h13-0/RoboCup/ImageProcessing/YoloFastest/chart.png

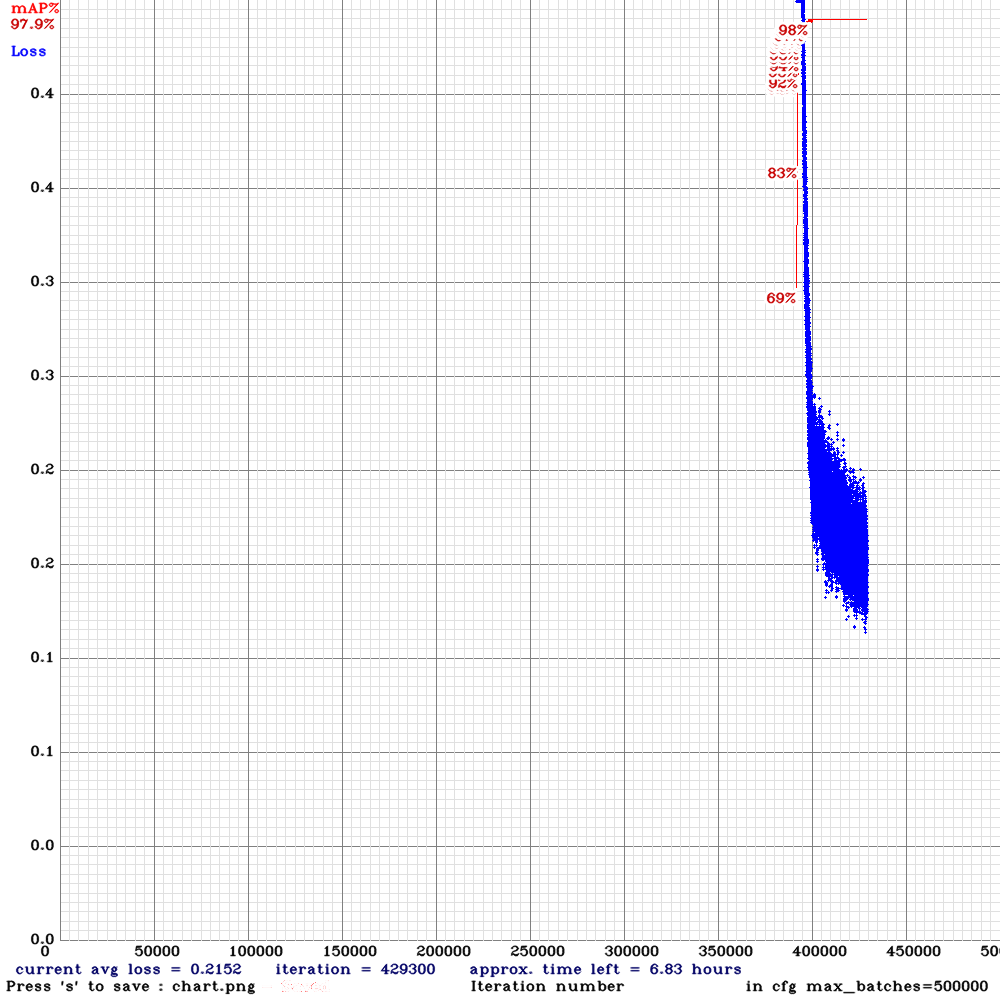
ImageProcessing/YoloFastest/chart.png
