h13-0/RoboCup/ImageProcessing/YoloV4Tiny/yoloV4TinyPreliminaryTrainWithHighBatch320/chart.png

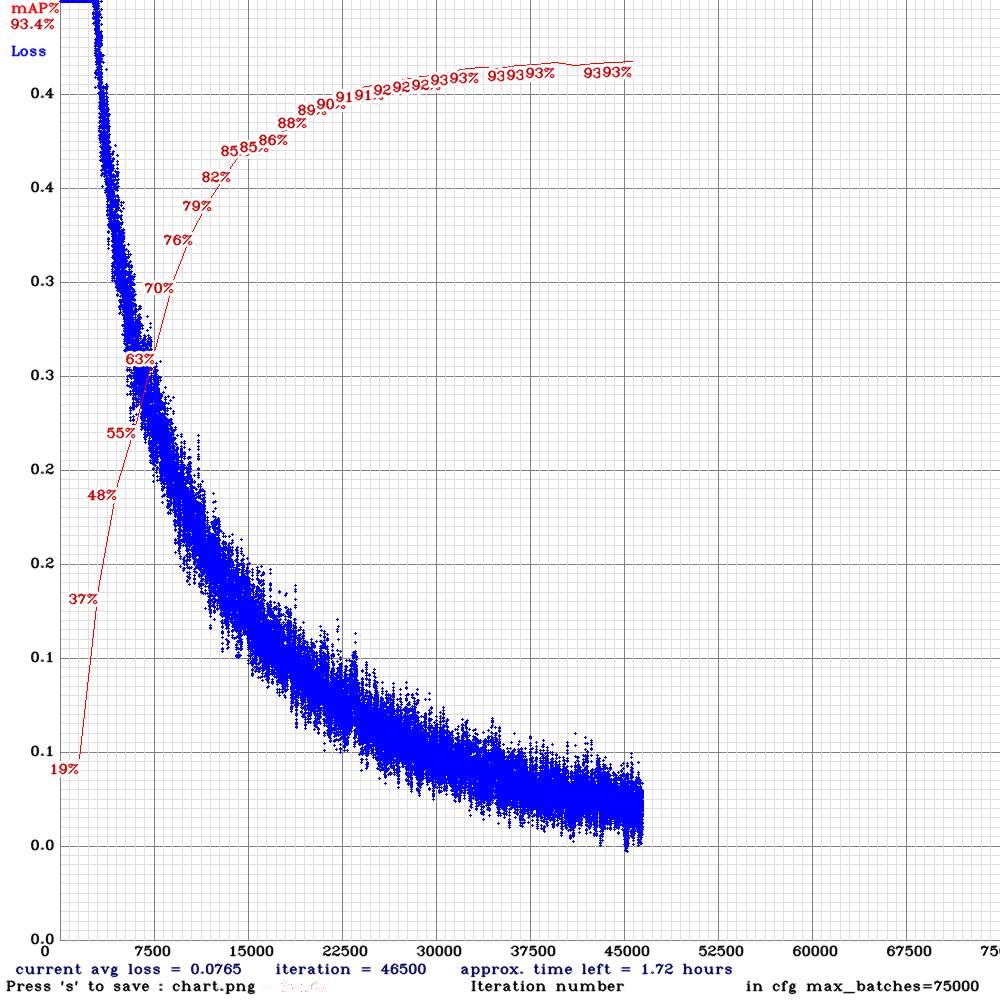
ImageProcessing/YoloV4Tiny/yoloV4TinyPreliminaryTrainWithHighBatch320/chart.png
