h13-0/RoboCup/ImageProcessing/YoloV4Tiny/yoloV4TinyRetrainWithRealScene320/predictions.jpg

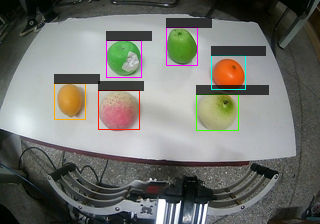
ImageProcessing/YoloV4Tiny/yoloV4TinyRetrainWithRealScene320/predictions.jpg
