h13-0/RoboCup/Images/LiftingPlatformAnnotationPicture1.jpg

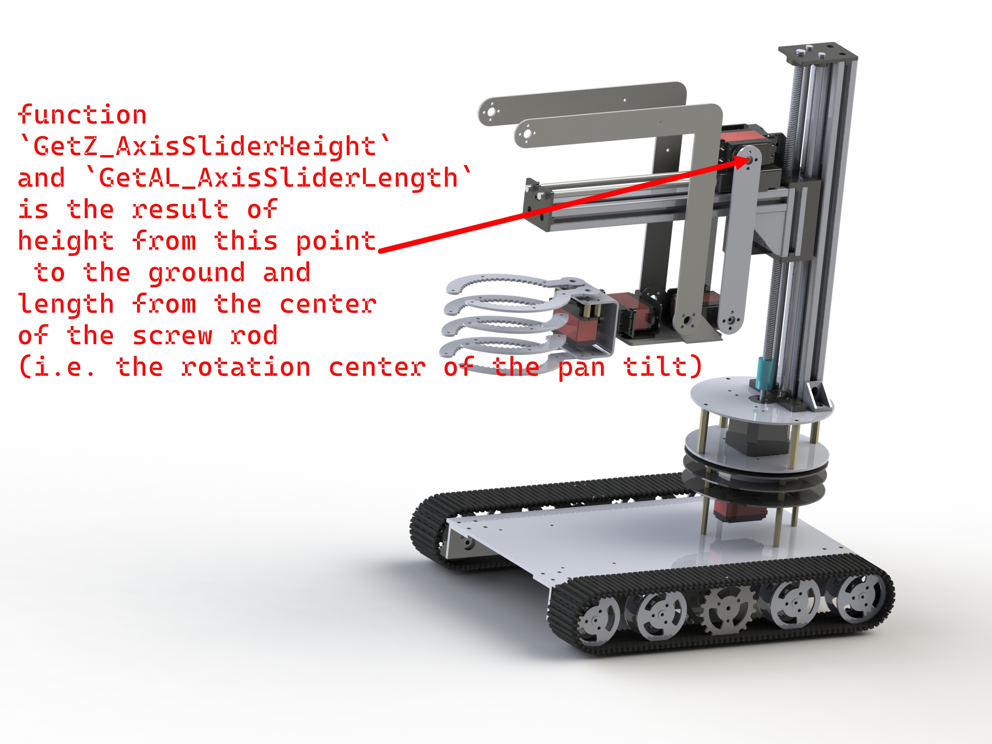
Images/LiftingPlatformAnnotationPicture1.jpg
