h13-0/RoboCup/Images/俯视图.JPG

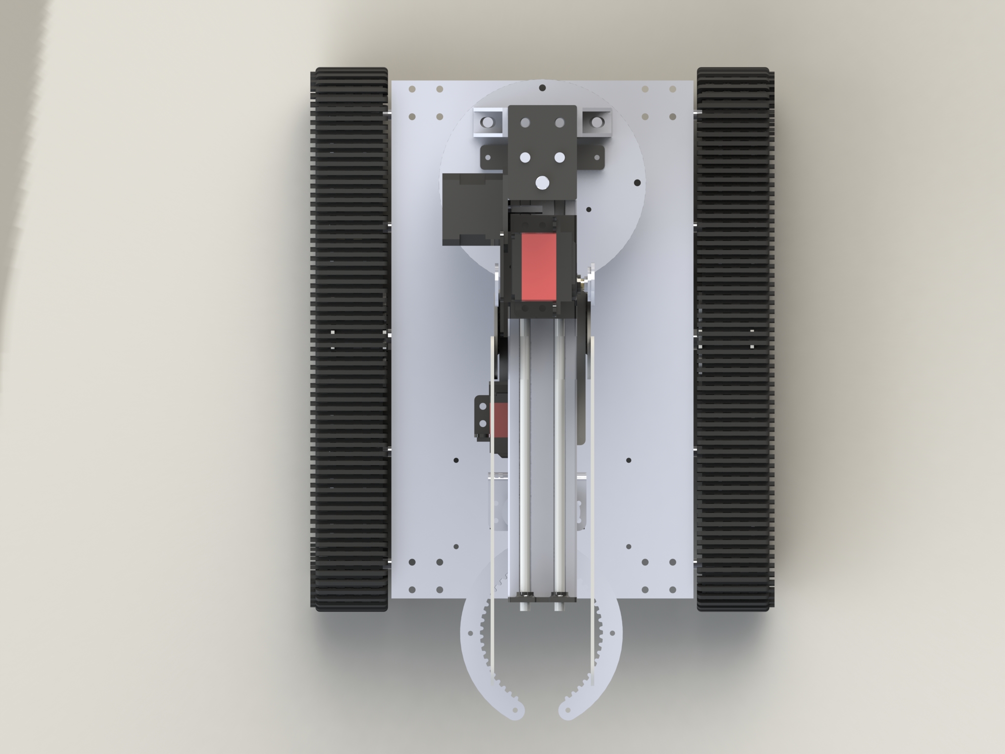
Images/俯视图.JPG
