h13-0/RoboCup/Images/左视图.JPG

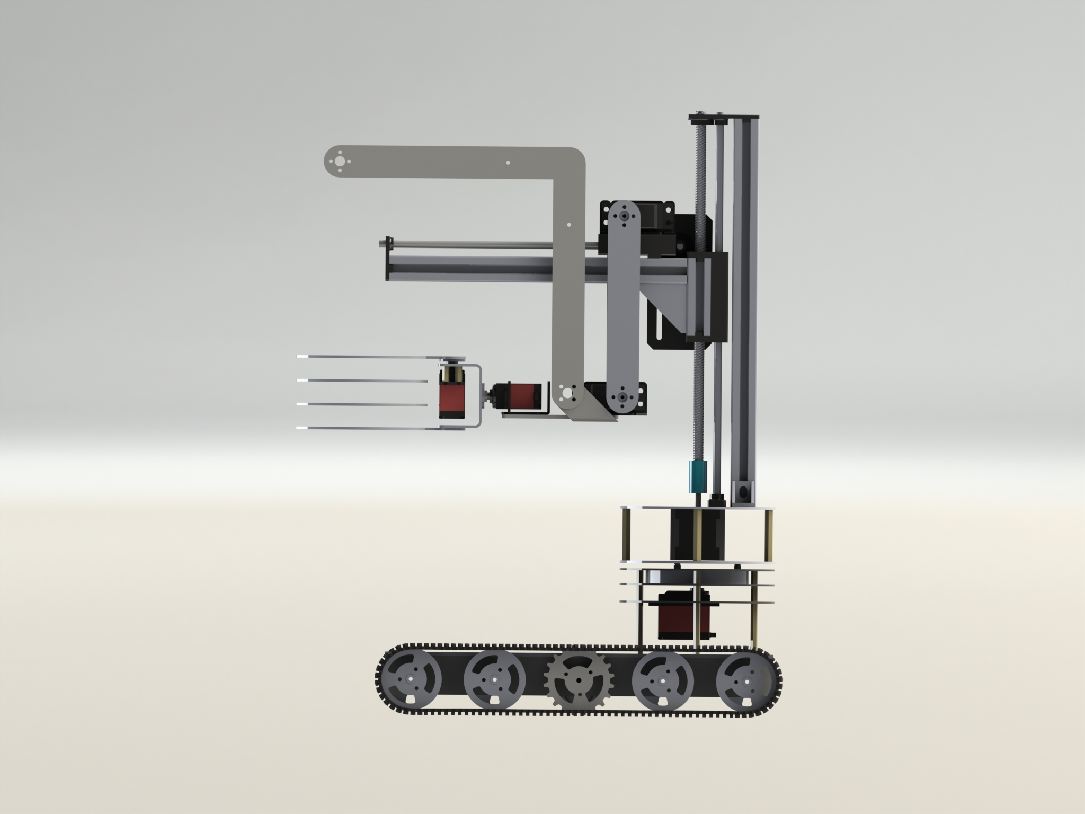
Images/左视图.JPG
