h13-0/RoboCup/Images/斜视图.JPG

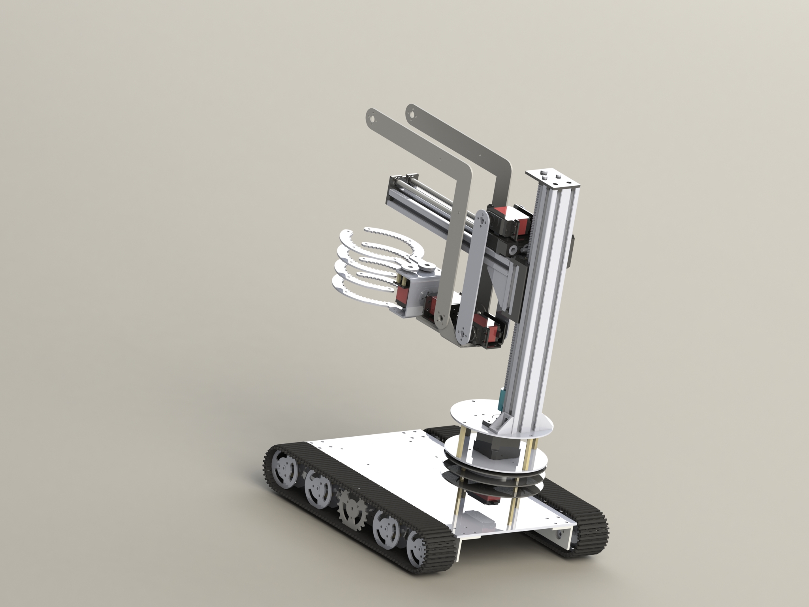
Images/斜视图.JPG
