h13-0/RoboCup/Machine/3D打印STL/磁铁竖向支架.STL

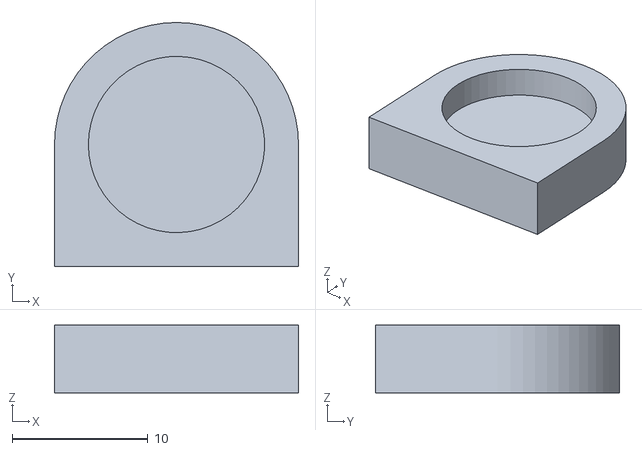
[picture p35: CAD file, 2021-08-29]
Machine/3D打印STL/磁铁竖向支架.STL
18.0 x 18.0 x 5.00
