h13-0/RoboCup/Machine/从动轮轴承.SLDPRT

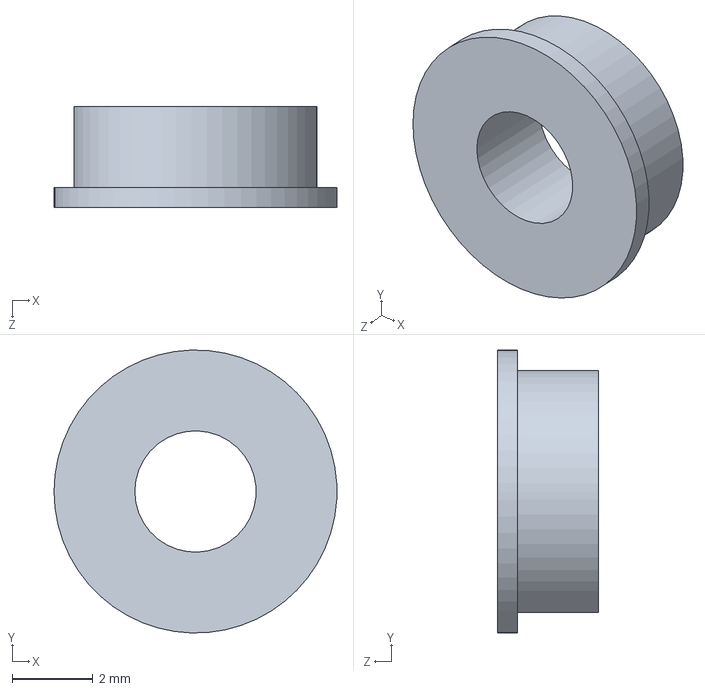
[picture p36: CAD file, 2022-04-09]
Machine/从动轮轴承.SLDPRT
7.00 x 7.00 x 2.50 mm
