h13-0/RoboCup/Machine/3D打印STL/霍尔传感器支架.STL

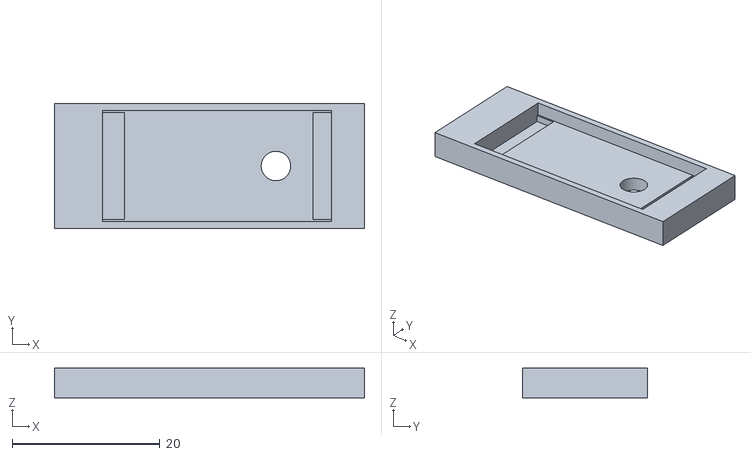
[picture p38: CAD file, 2021-08-29]
Machine/3D打印STL/霍尔传感器支架.STL
42.0 x 17.0 x 4.00
