h13-0/RoboCup/Machine/3429电机.SLDPRT

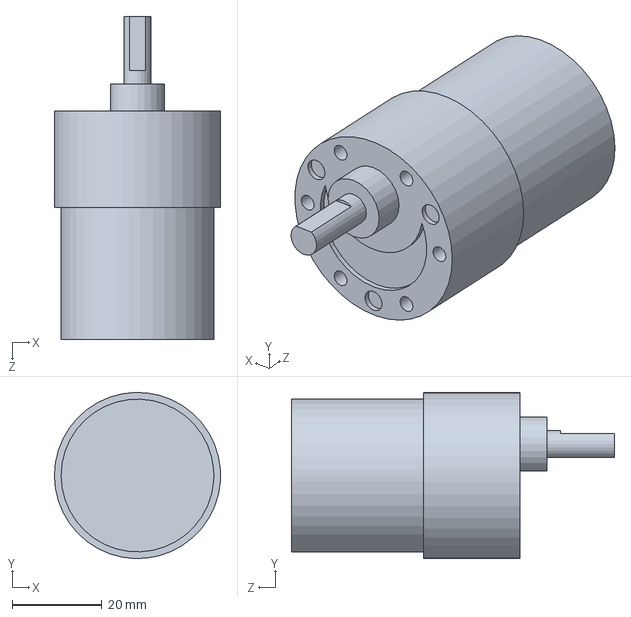
[picture p40: CAD file, 2022-04-09]
Machine/3429电机.SLDPRT
37.0 x 37.0 x 71.9 mm
