h13-0/RoboCup/Machine/3D打印STL/丝杆底支架.STL

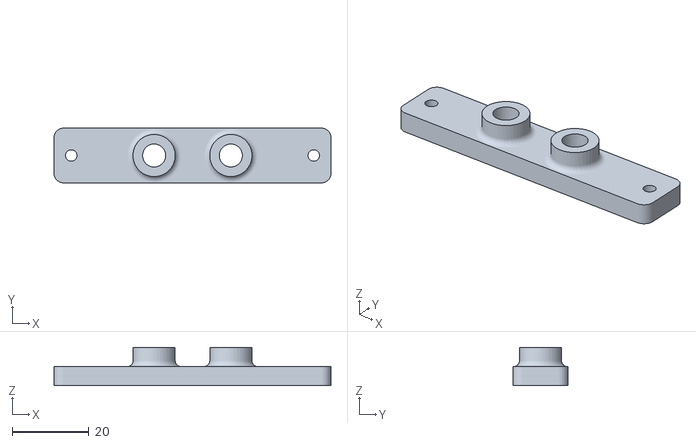
[picture p41: CAD file, 2021-08-23]
Machine/3D打印STL/丝杆底支架.STL
72.2 x 14.3 x 10.0
