h13-0/RoboCup/Machine/3D打印STL/丝杆滑块.STL

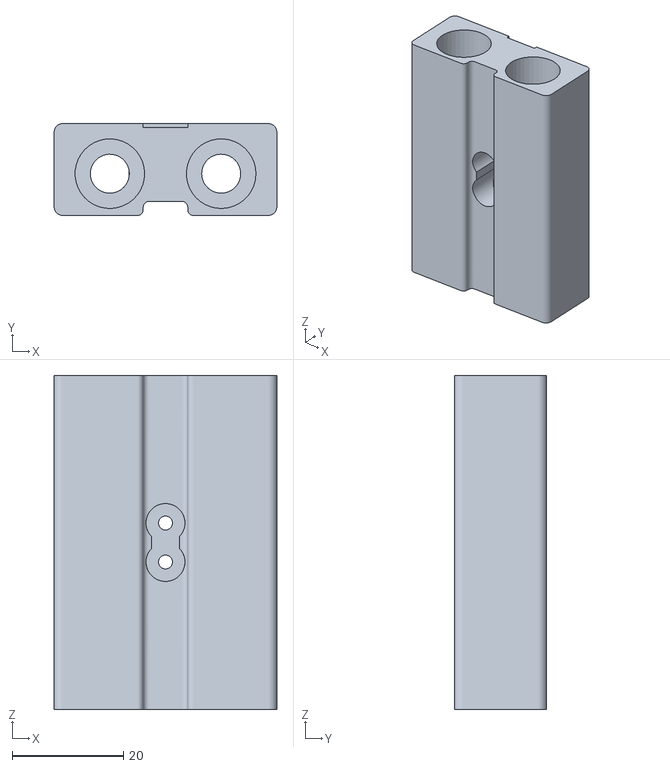
[picture p42: CAD file, 2021-08-23]
Machine/3D打印STL/丝杆滑块.STL
40.0 x 16.5 x 60.0
