h13-0/RoboCup/Machine/从动轮支杆.SLDPRT

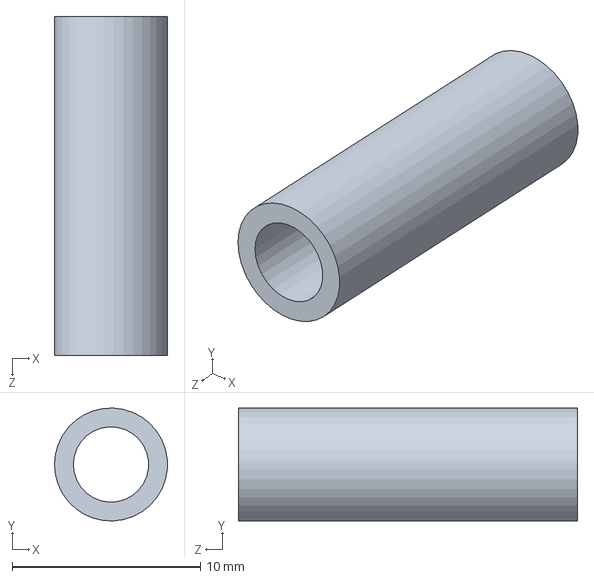
[picture p43: CAD file, 2022-04-09]
Machine/从动轮支杆.SLDPRT
6.00 x 5.99 x 18.0 mm
