h13-0/RoboCup/Machine/3D打印STL/直线轴承支架.STL

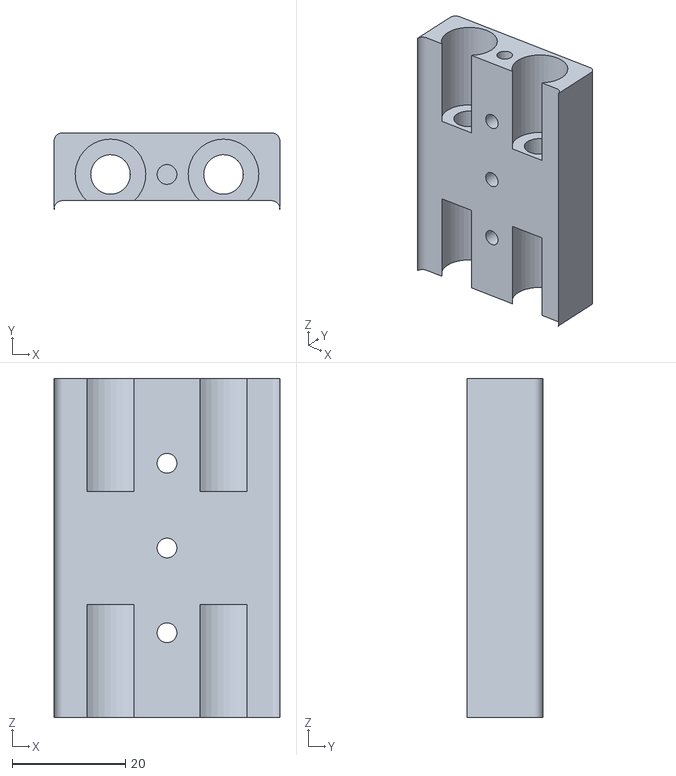
[picture p44: CAD file, 2021-08-23]
Machine/3D打印STL/直线轴承支架.STL
40.0 x 13.5 x 60.0
