h13-0/RoboCup/Machine/42步进.SLDPRT

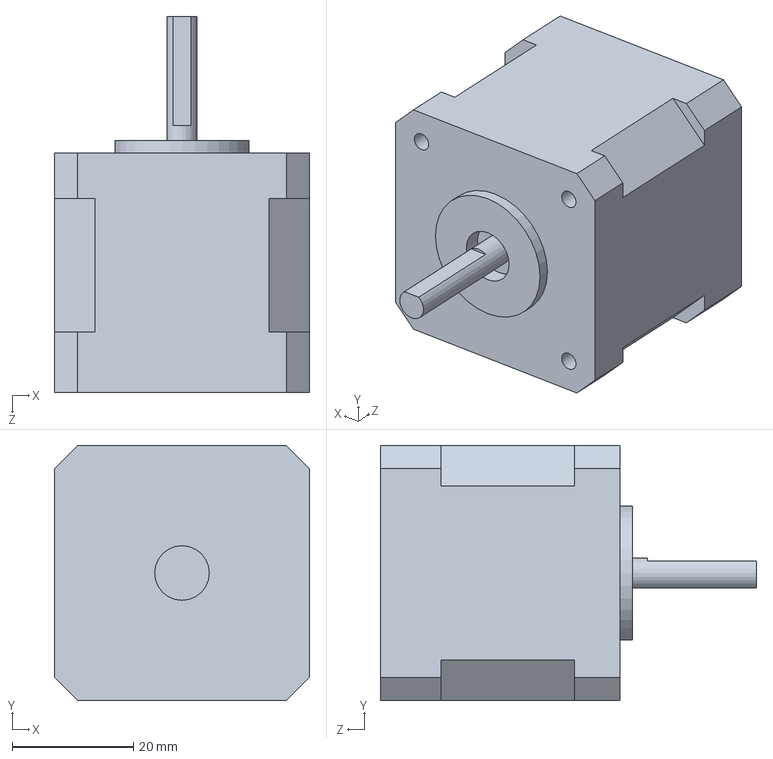
[picture p45: CAD file, 2022-04-09]
Machine/42步进.SLDPRT
42.0 x 42.0 x 62.0 mm
