h13-0/RoboCup/Machine/3D打印STL/侧TOF支架.STL

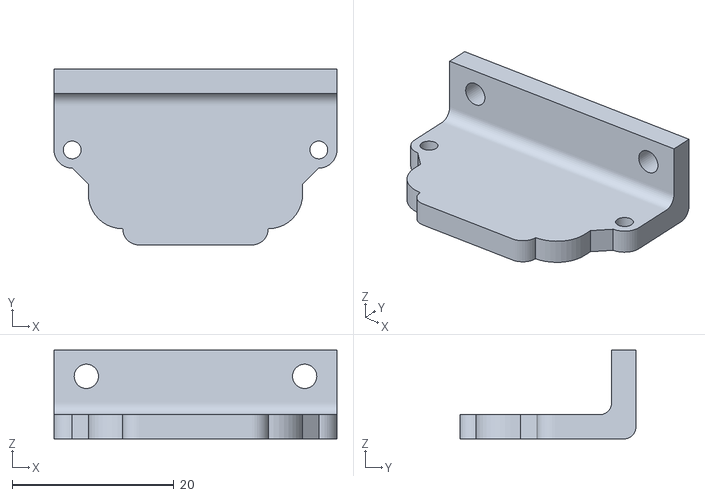
[picture p46: CAD file, 2021-08-23]
Machine/3D打印STL/侧TOF支架.STL
35.0 x 21.8 x 11.0
