h13-0/RoboCup/Machine/3D打印STL/丝杆顶支架.STL

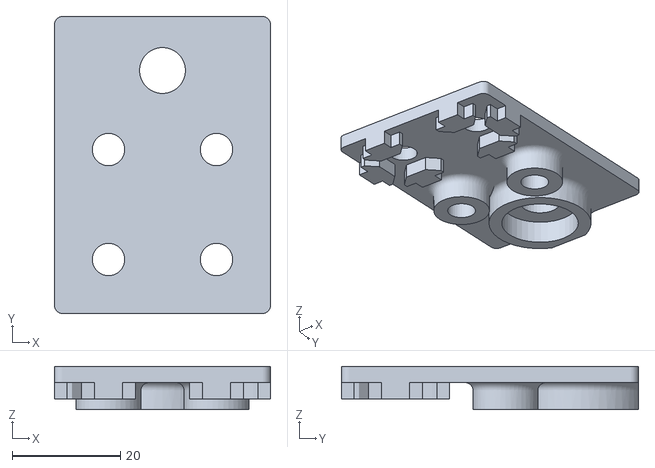
[picture p47: CAD file, 2021-08-23]
Machine/3D打印STL/丝杆顶支架.STL
40.0 x 55.0 x 8.00
