h13-0/RoboCup/Machine/M4铜柱40mm.SLDPRT

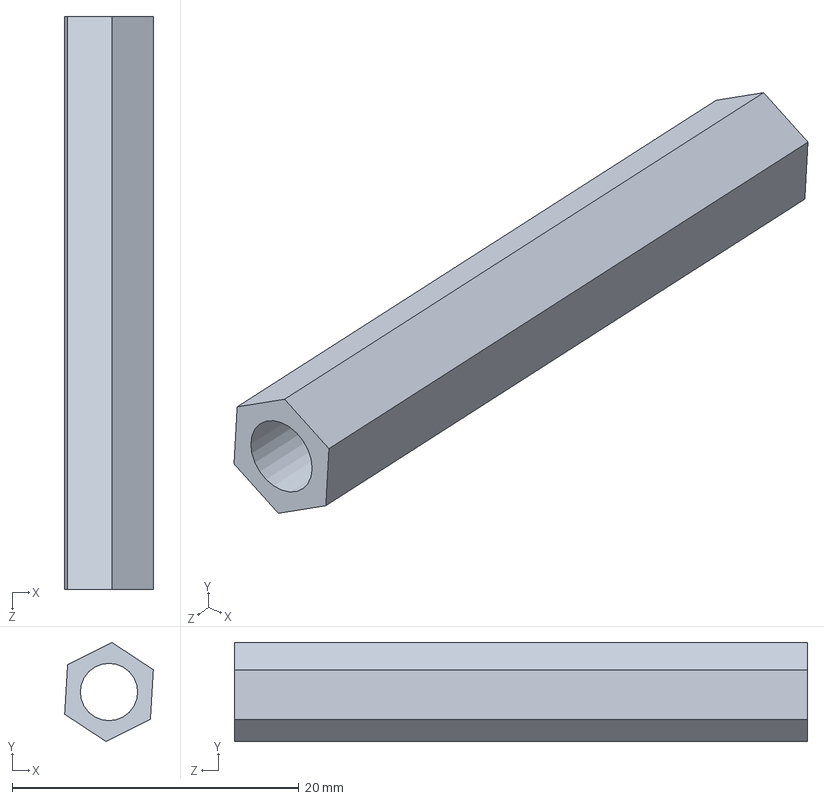
[picture p48: CAD file, 2022-04-09]
Machine/M4铜柱40mm.SLDPRT
6.19 x 6.92 x 40.0 mm
