h13-0/RoboCup/Machine/3D打印STL/丝杆滑台外支架.STL

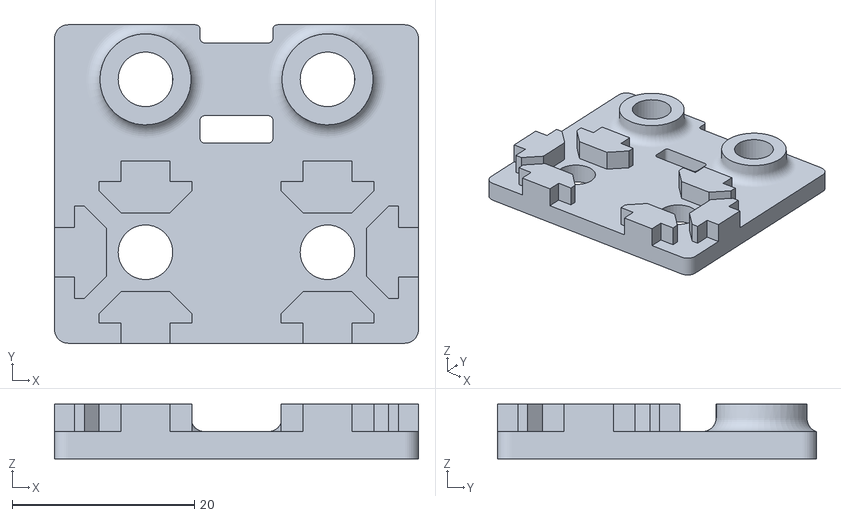
[picture p49: CAD file, 2021-08-23]
Machine/3D打印STL/丝杆滑台外支架.STL
40.0 x 35.0 x 6.00
