h13-0/RoboCup/Machine/M3紧固螺丝.SLDPRT

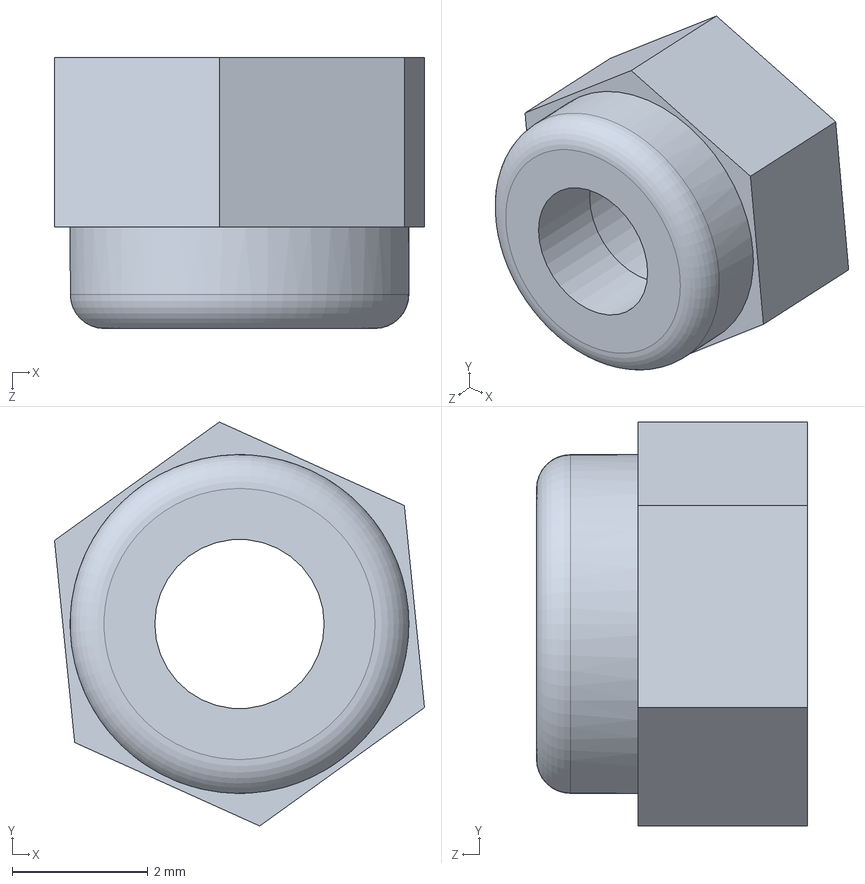
[picture p50: CAD file, 2022-04-09]
Machine/M3紧固螺丝.SLDPRT
5.46 x 5.96 x 4.00 mm
