h13-0/RoboCup/Machine/2040铝型材300mm.SLDPRT

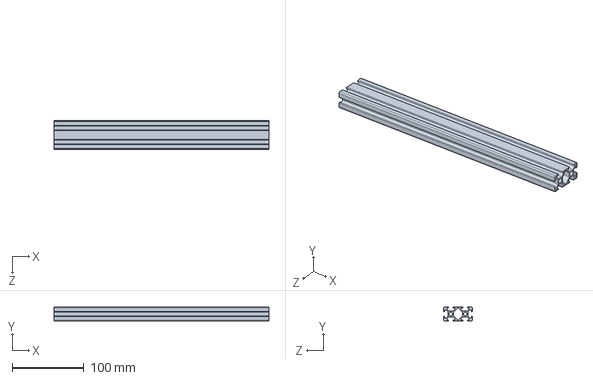
[picture p51: CAD file, 2022-04-09]
Machine/2040铝型材300mm.SLDPRT
300.0 x 20.0 x 40.0 mm
