h13-0/RoboCup/Machine/3D打印STL/同步带轴承支架.STL

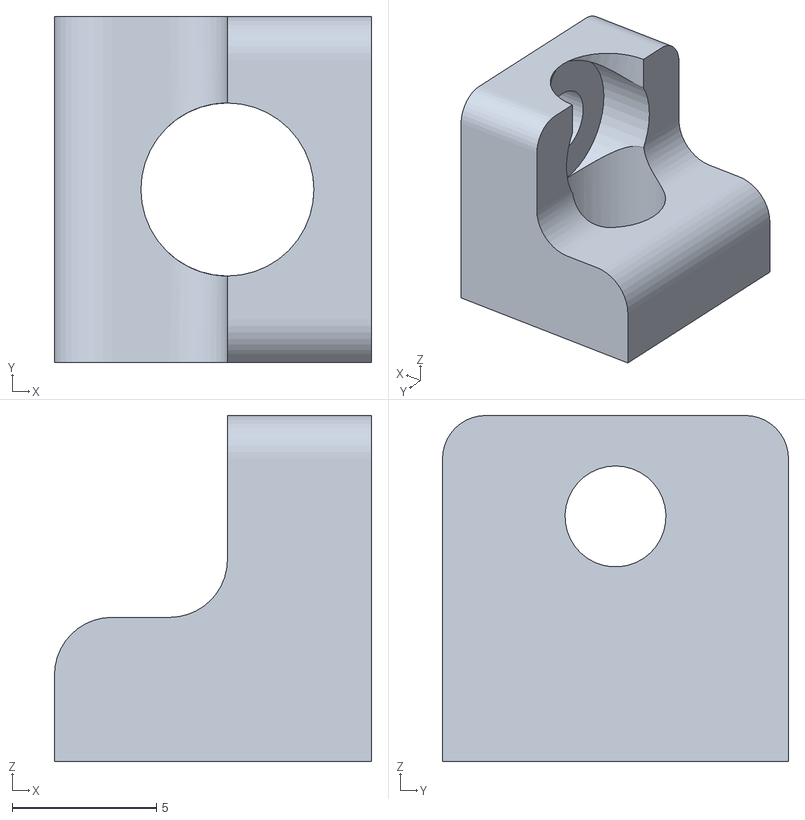
[picture p52: CAD file, 2021-08-23]
Machine/3D打印STL/同步带轴承支架.STL
11.0 x 12.0 x 12.0
