h13-0/RoboCup/Machine/3D打印STL/丝杆螺母支架.STL

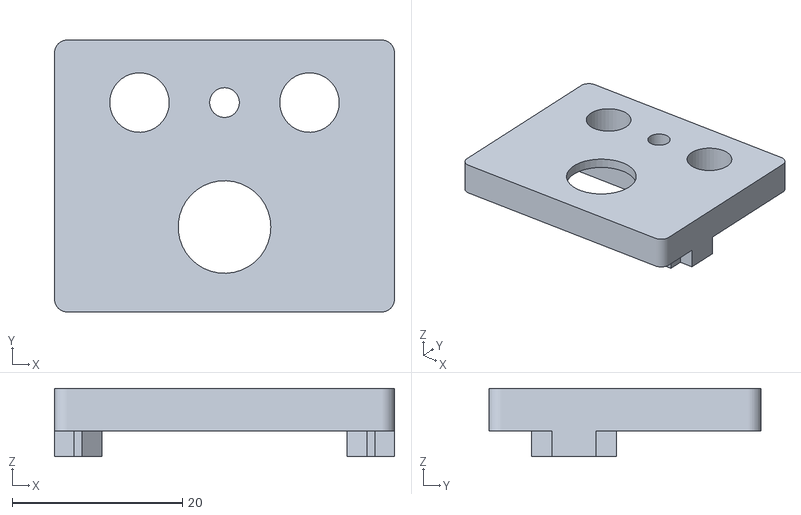
[picture p53: CAD file, 2021-08-23]
Machine/3D打印STL/丝杆螺母支架.STL
40.0 x 32.0 x 8.00
