h13-0/RoboCup/Machine/3D打印STL/电池垫板.STL

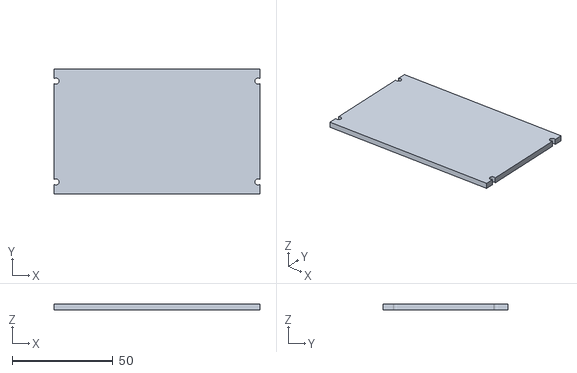
[picture p54: CAD file, 2021-08-23]
Machine/3D打印STL/电池垫板.STL
102.0 x 62.0 x 3.00
