h13-0/RoboCup/Machine/6mm滑杆307mm.SLDPRT

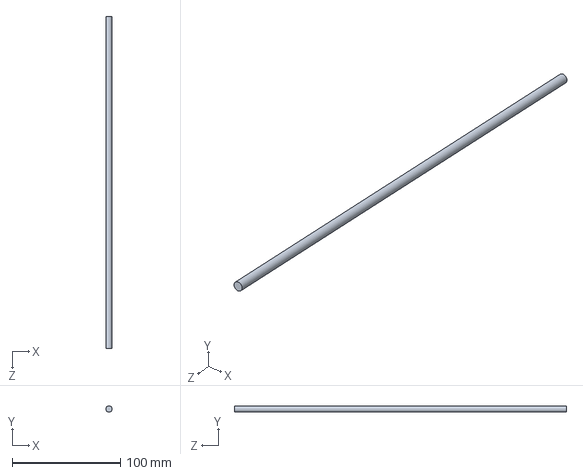
[picture p55: CAD file, 2022-04-09]
Machine/6mm滑杆307mm.SLDPRT
6.00 x 6.00 x 307.0 mm
