h13-0/RoboCup/Machine/3D打印STL/丝杆滑台内支架.STL

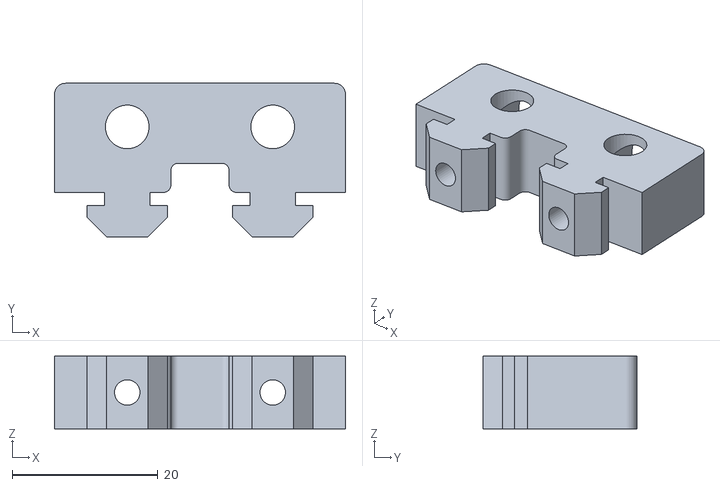
[picture p56: CAD file, 2021-08-23]
Machine/3D打印STL/丝杆滑台内支架.STL
40.0 x 21.1 x 10.0
