h13-0/RoboCup/Machine/M4大垫片.SLDPRT

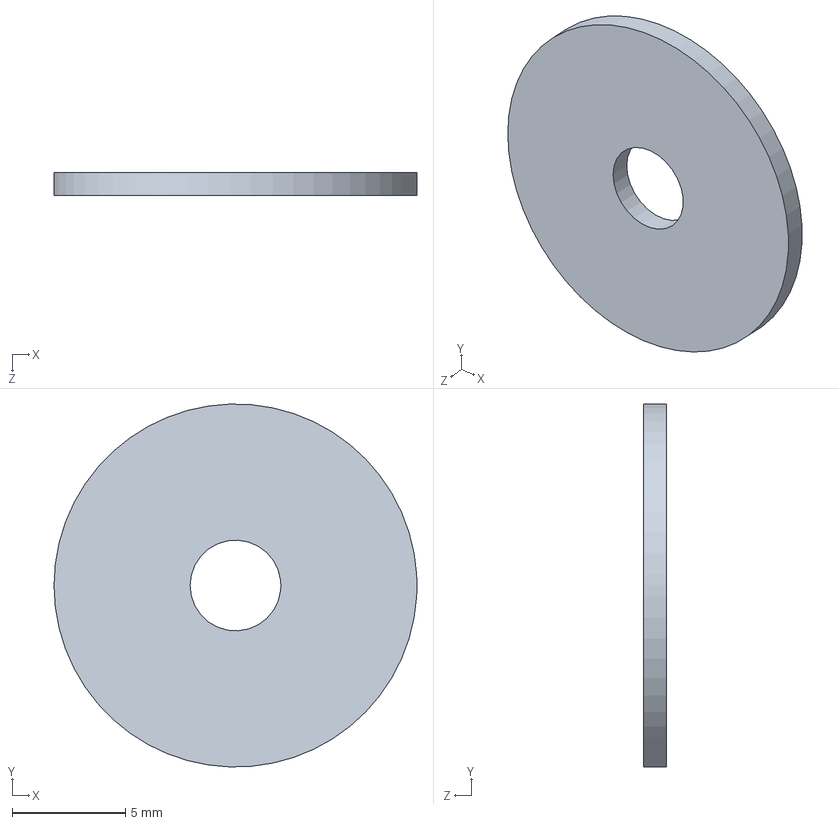
[picture p57: CAD file, 2022-04-09]
Machine/M4大垫片.SLDPRT
16.0 x 16.0 x 1.00 mm
