h13-0/RoboCup/Machine/3D打印STL/TOFSuppter.STL

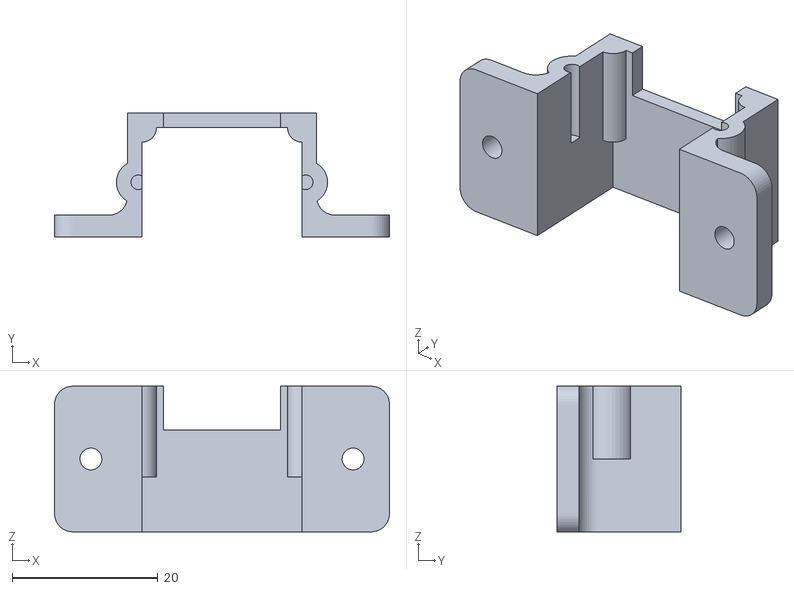
[picture p58: CAD file, 2021-06-14]
Machine/3D打印STL/TOFSuppter.STL
46.0 x 17.0 x 20.0
