h13-0/RoboCup/Machine/电机支架.SLDPRT

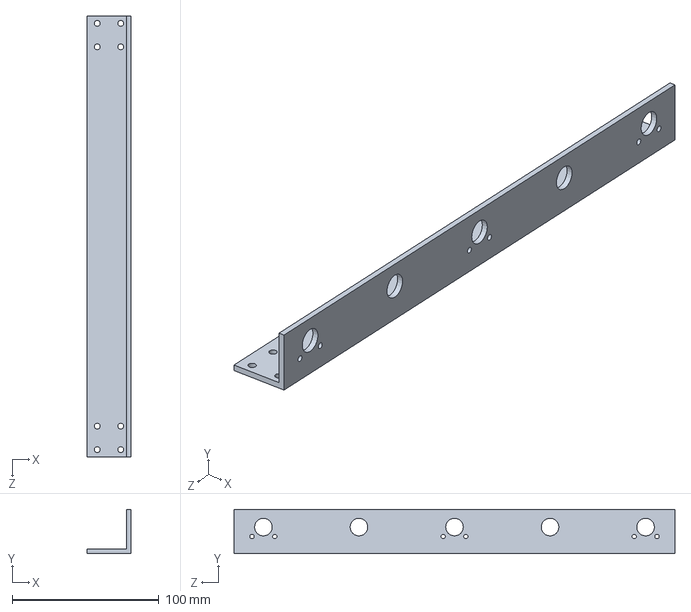
[picture p59: CAD file, 2022-04-09]
Machine/电机支架.SLDPRT
30.0 x 30.0 x 300.0 mm
