h13-0/RoboCup/Machine/M3铜柱10mm.SLDPRT

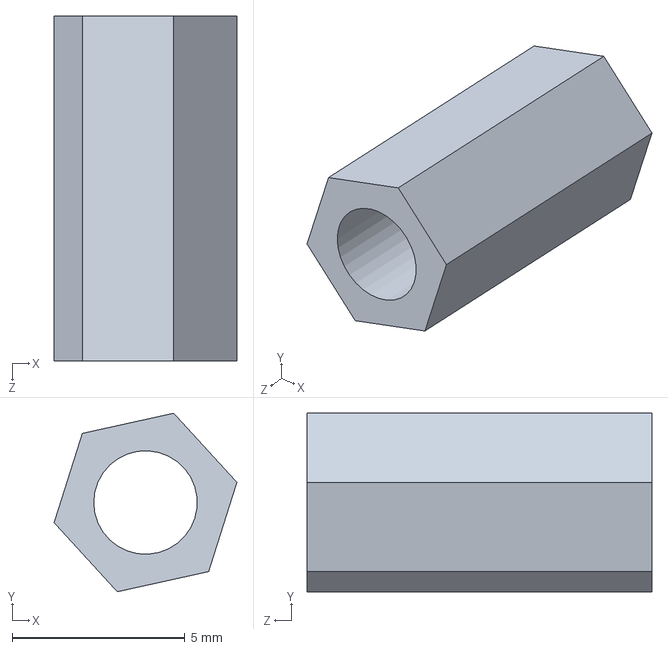
[picture p60: CAD file, 2022-04-09]
Machine/M3铜柱10mm.SLDPRT
5.30 x 5.17 x 10.0 mm
