h13-0/RoboCup/Machine/42步进35mm.SLDPRT

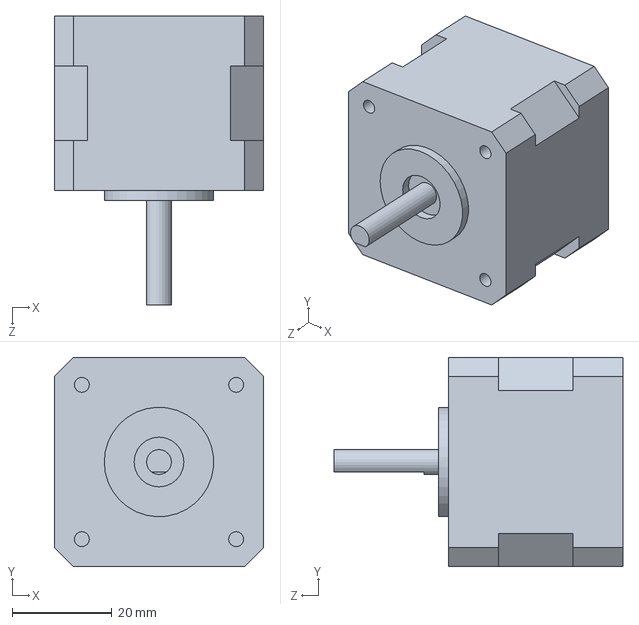
[picture p61: CAD file, 2022-04-09]
Machine/42步进35mm.SLDPRT
42.0 x 42.0 x 58.0 mm
