h13-0/RoboCup/Machine/8mm丝杆轴承.SLDPRT

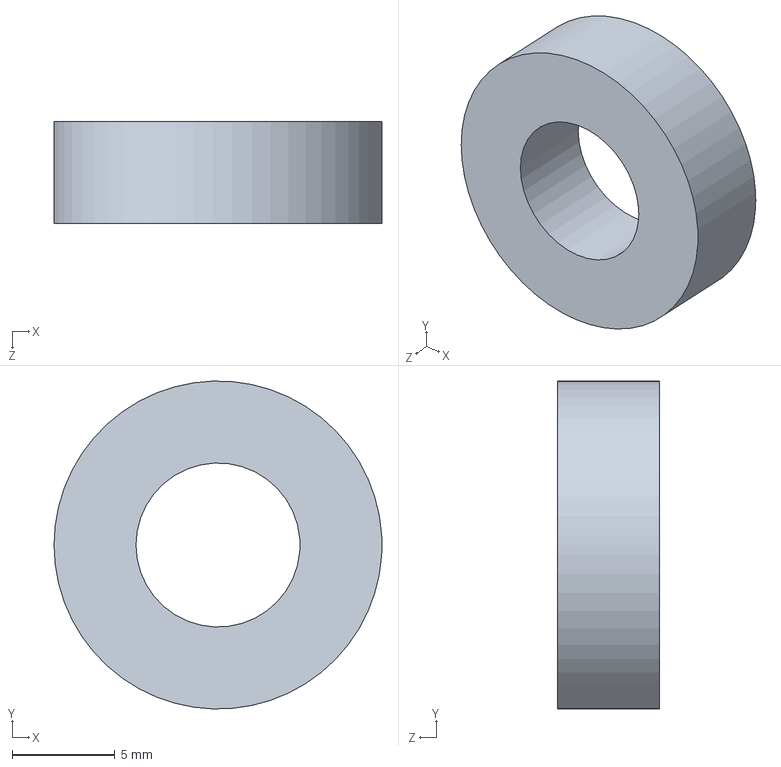
[picture p62: CAD file, 2022-04-09]
Machine/8mm丝杆轴承.SLDPRT
16.0 x 16.0 x 5.00 mm
