h13-0/RoboCup/Machine/42步进支架.SLDPRT

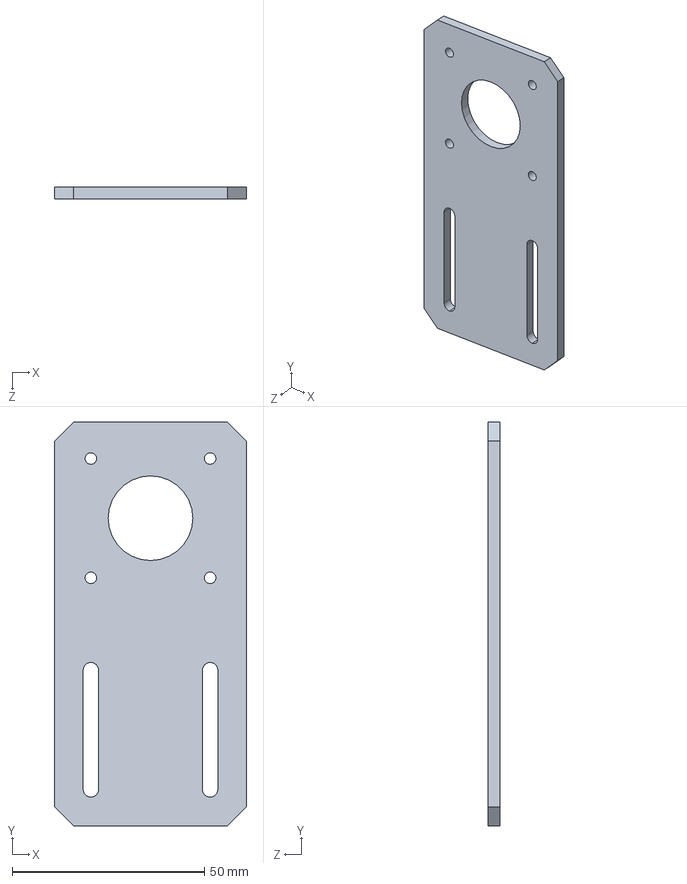
[picture p63: CAD file, 2022-04-09]
Machine/42步进支架.SLDPRT
50.0 x 105.0 x 3.00 mm
