h13-0/RoboCup/Machine/6mm滑杆220mm.SLDPRT

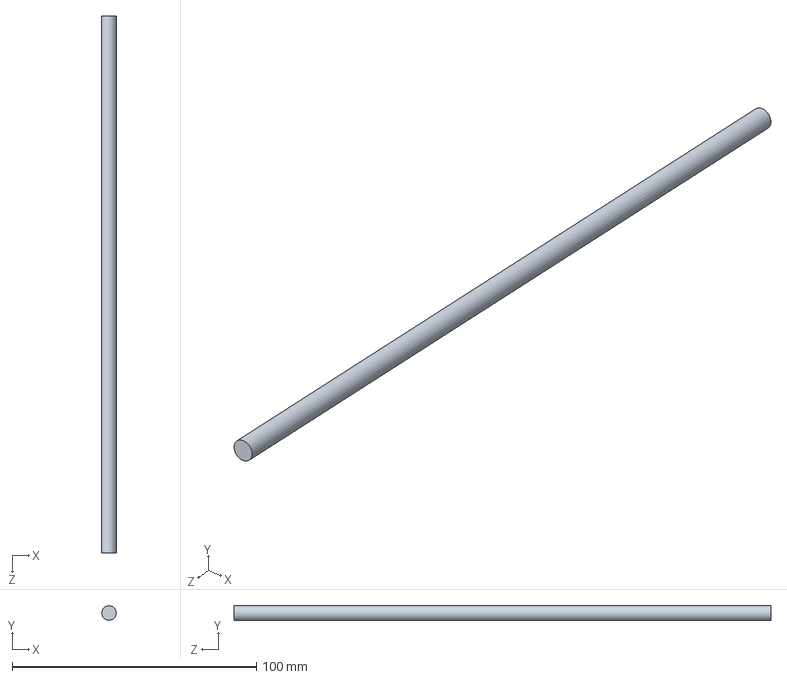
[picture p64: CAD file, 2022-04-09]
Machine/6mm滑杆220mm.SLDPRT
6.00 x 6.00 x 220.0 mm
