h13-0/RoboCup/Machine/M3铜柱17mm.SLDPRT

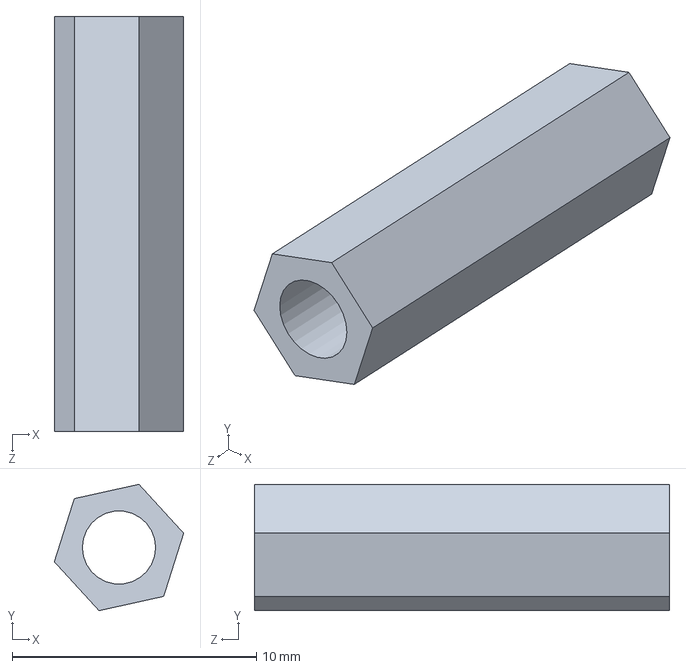
[picture p65: CAD file, 2022-04-09]
Machine/M3铜柱17mm.SLDPRT
5.30 x 5.17 x 17.0 mm
