h13-0/RoboCup/Machine/舵机圆盘.SLDPRT

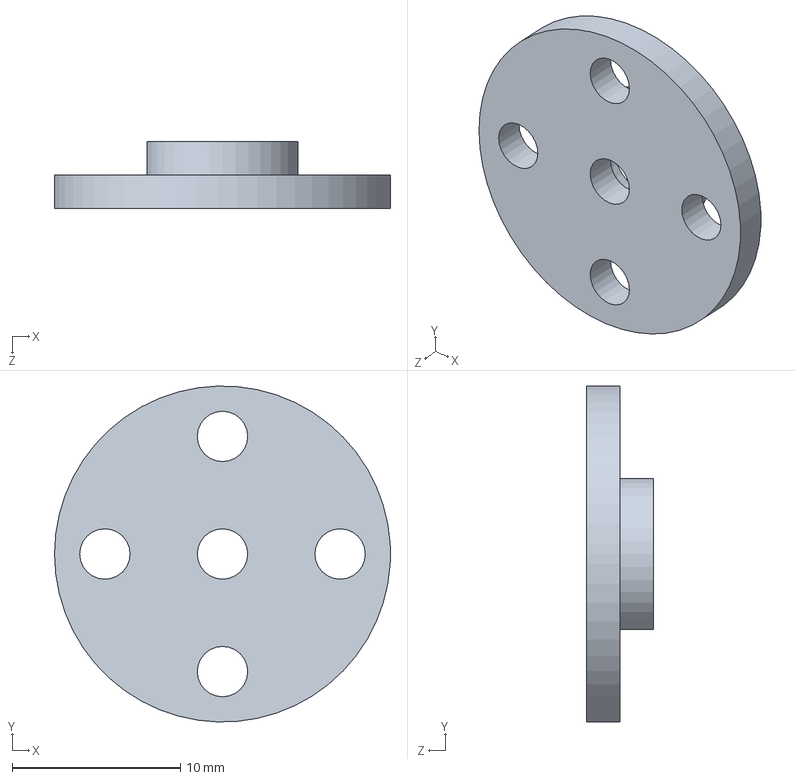
[picture p66: CAD file, 2022-04-09]
Machine/舵机圆盘.SLDPRT
20.0 x 20.0 x 4.00 mm
