h13-0/RoboCup/Machine/2040铝型材230mm.SLDPRT

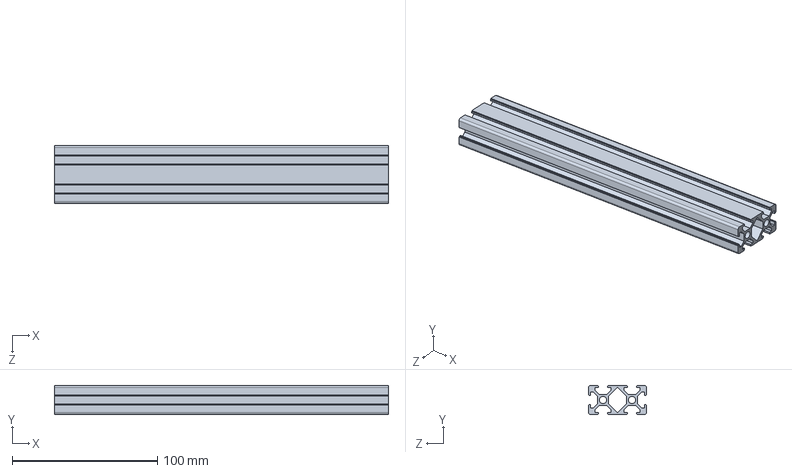
[picture p67: CAD file, 2022-04-09]
Machine/2040铝型材230mm.SLDPRT
230.0 x 20.0 x 40.0 mm
