h13-0/RoboCup/Machine/M3铜柱39.5mm.SLDPRT

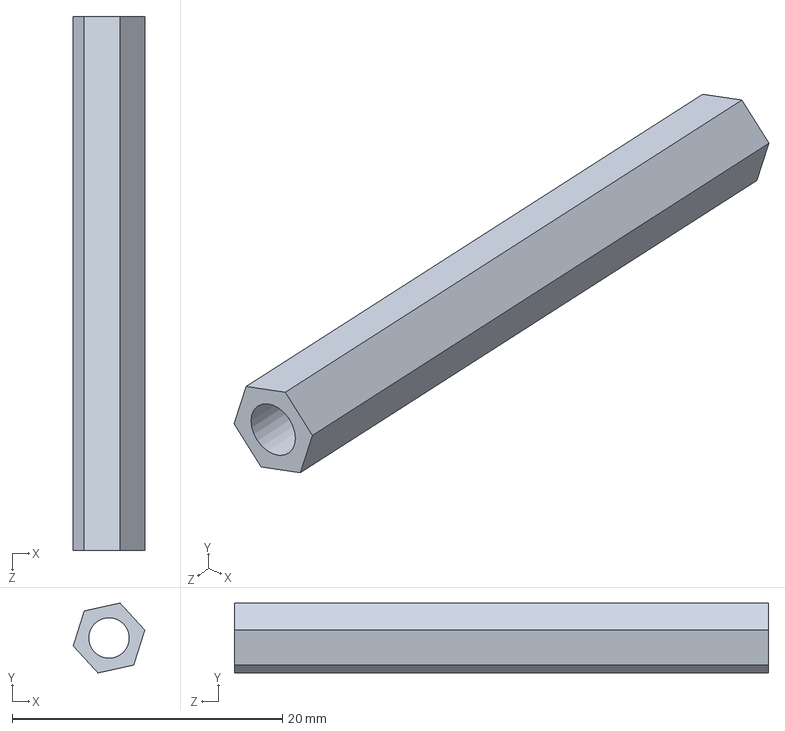
[picture p68: CAD file, 2022-04-09]
Machine/M3铜柱39.5mm.SLDPRT
5.30 x 5.17 x 39.5 mm
