h13-0/RoboCup/Machine/2020角件.SLDPRT

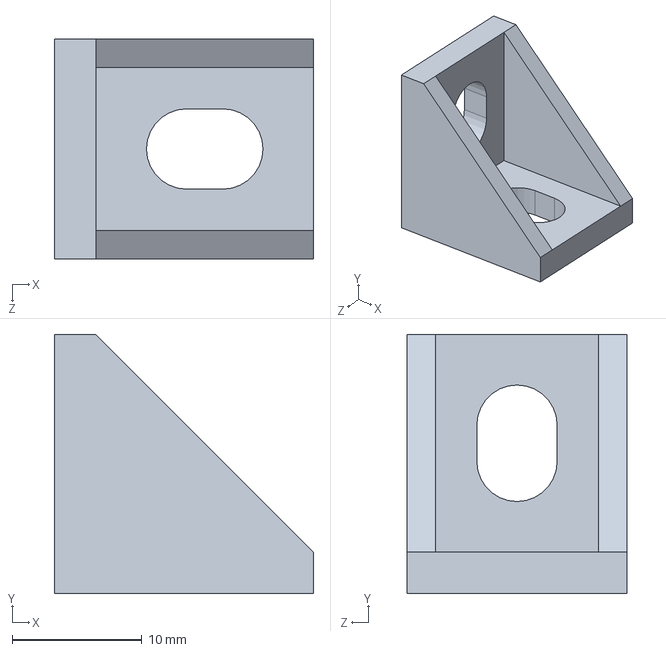
[picture p69: CAD file, 2022-04-09]
Machine/2020角件.SLDPRT
20.0 x 20.0 x 17.0 mm
