h13-0/RoboCup/Machine/从动轮间隔杆.SLDPRT

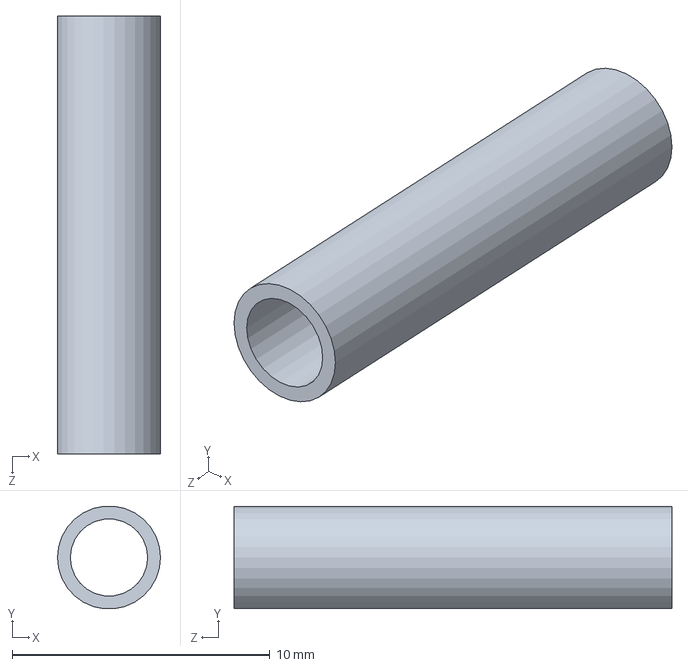
[picture p70: CAD file, 2022-04-09]
Machine/从动轮间隔杆.SLDPRT
4.00 x 3.98 x 17.0 mm
