h13-0/RoboCup/Machine/2040角件.SLDPRT

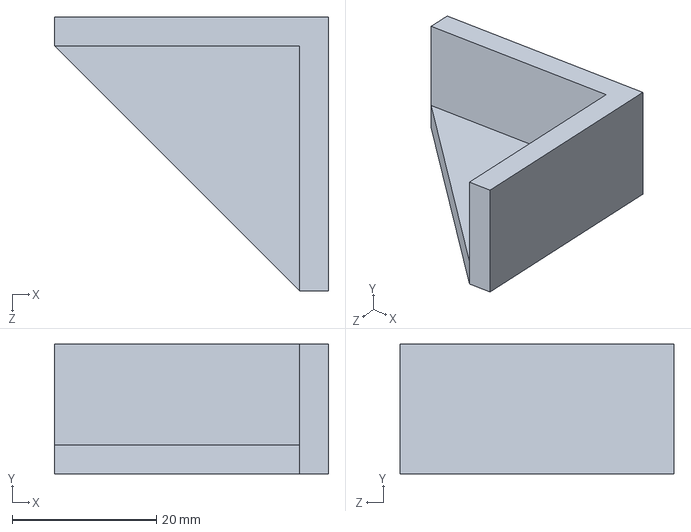
[picture p71: CAD file, 2022-04-09]
Machine/2040角件.SLDPRT
38.0 x 18.0 x 38.0 mm
