h13-0/RoboCup/Machine/车板铝板.SLDPRT

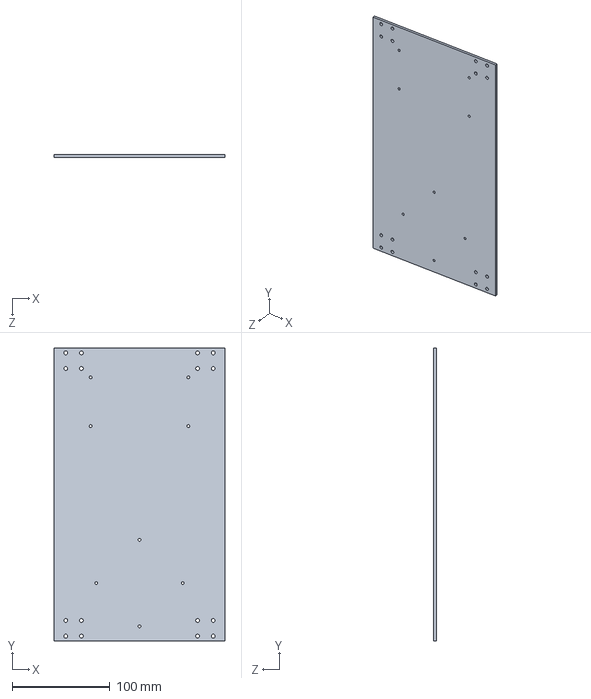
[picture p72: CAD file, 2022-04-09]
Machine/车板铝板.SLDPRT
175.0 x 300.0 x 3.00 mm
