h13-0/RoboCup/Machine/16齿同步轮.SLDPRT

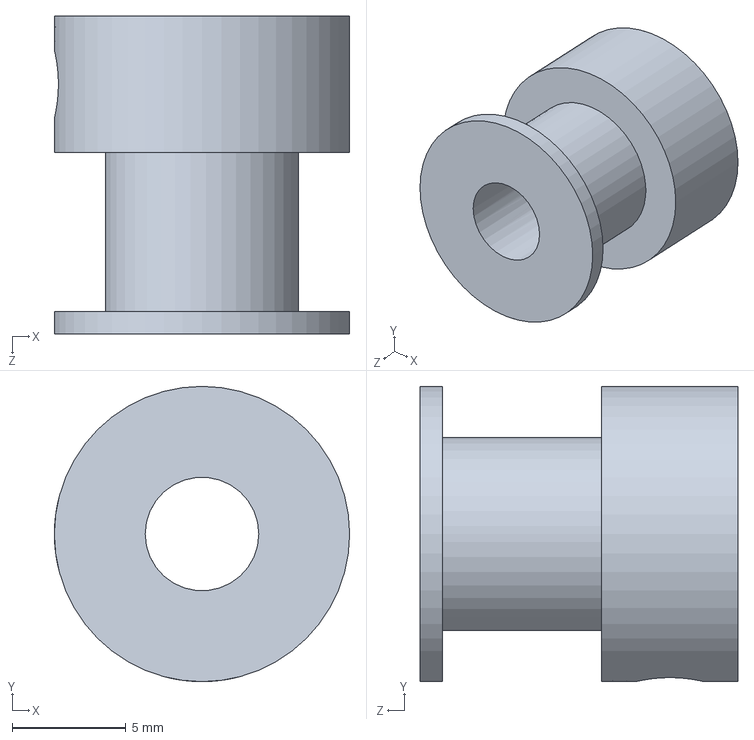
[picture p73: CAD file, 2022-04-09]
Machine/16齿同步轮.SLDPRT
13.0 x 13.0 x 14.0 mm
