h13-0/RoboCup/Machine/舵机斜U支架.SLDPRT

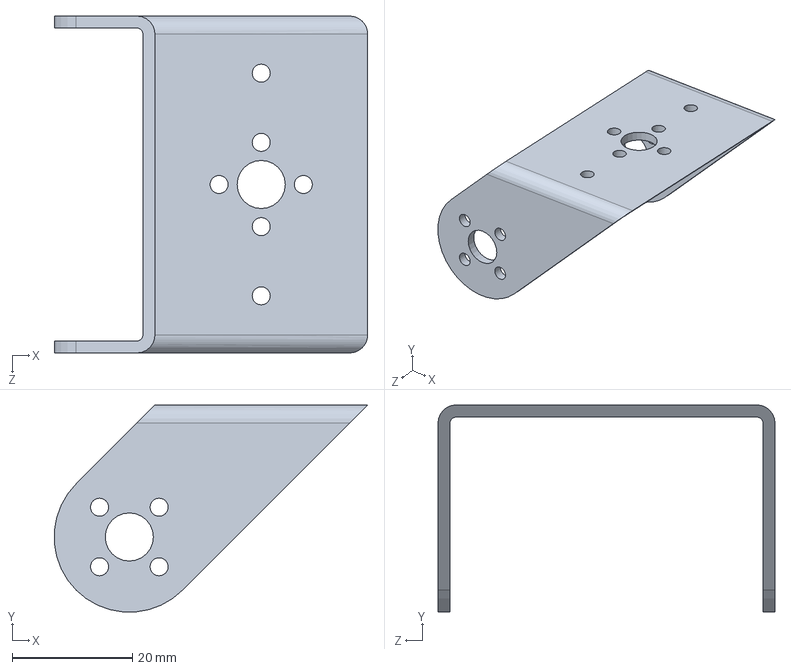
[picture p74: CAD file, 2022-04-09]
Machine/舵机斜U支架.SLDPRT
52.1 x 34.4 x 56.0 mm
