h13-0/RoboCup/Machine/M3铜柱32mm.SLDPRT

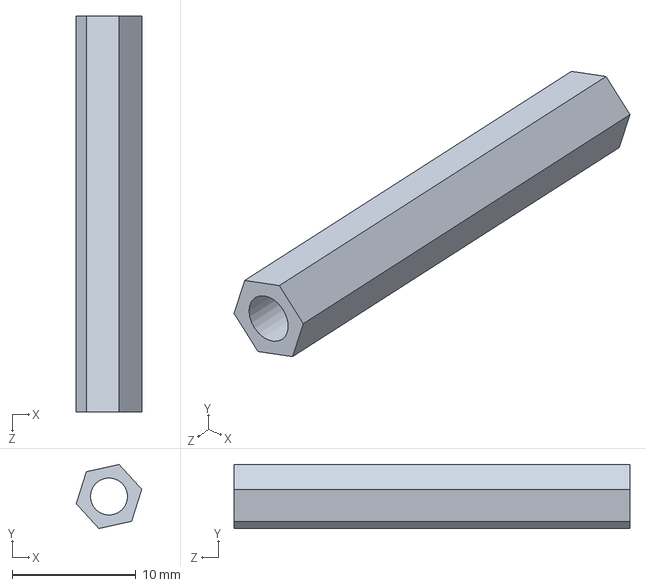
[picture p75: CAD file, 2022-04-09]
Machine/M3铜柱32mm.SLDPRT
5.30 x 5.17 x 32.0 mm
