h13-0/RoboCup/Machine/L形件.SLDPRT

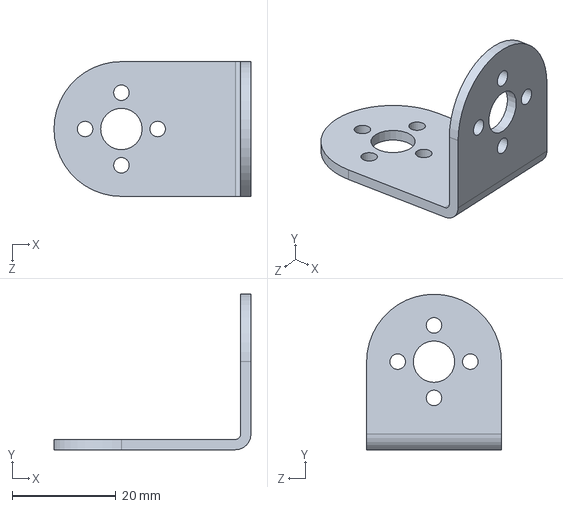
[picture p76: CAD file, 2022-04-09]
Machine/L形件.SLDPRT
38.0 x 30.0 x 26.0 mm
