h13-0/RoboCup/Machine/8mmx4丝杆285mm.SLDPRT

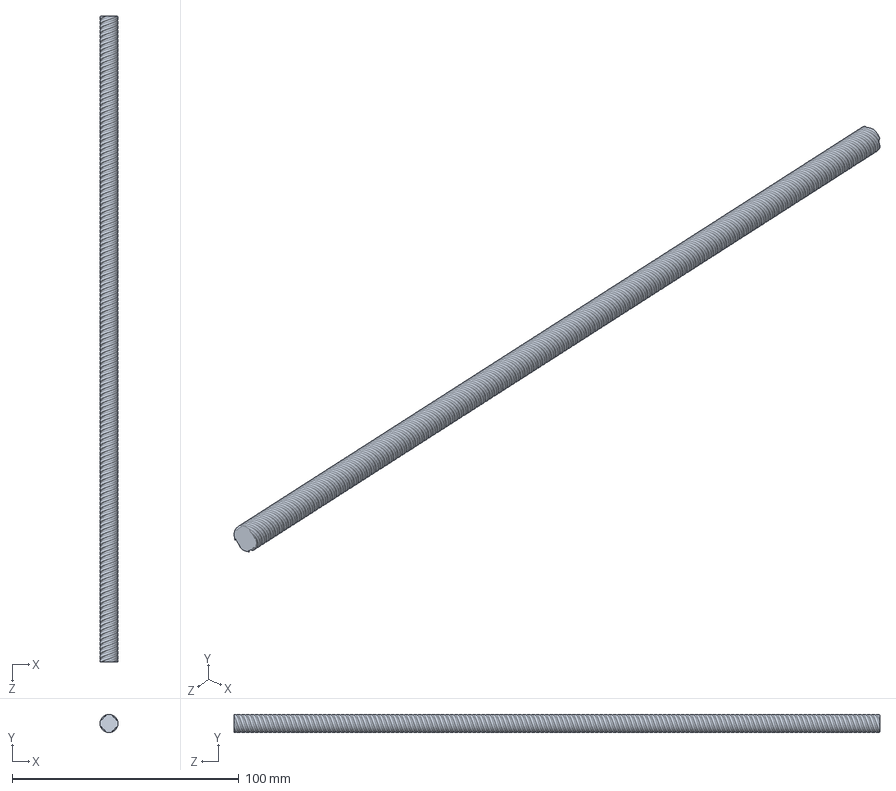
[picture p77: CAD file, 2022-04-09]
Machine/8mmx4丝杆285mm.SLDPRT
8.00 x 8.00 x 285.0 mm
