h13-0/RoboCup/Machine/6mm滑杆直线轴承.SLDPRT

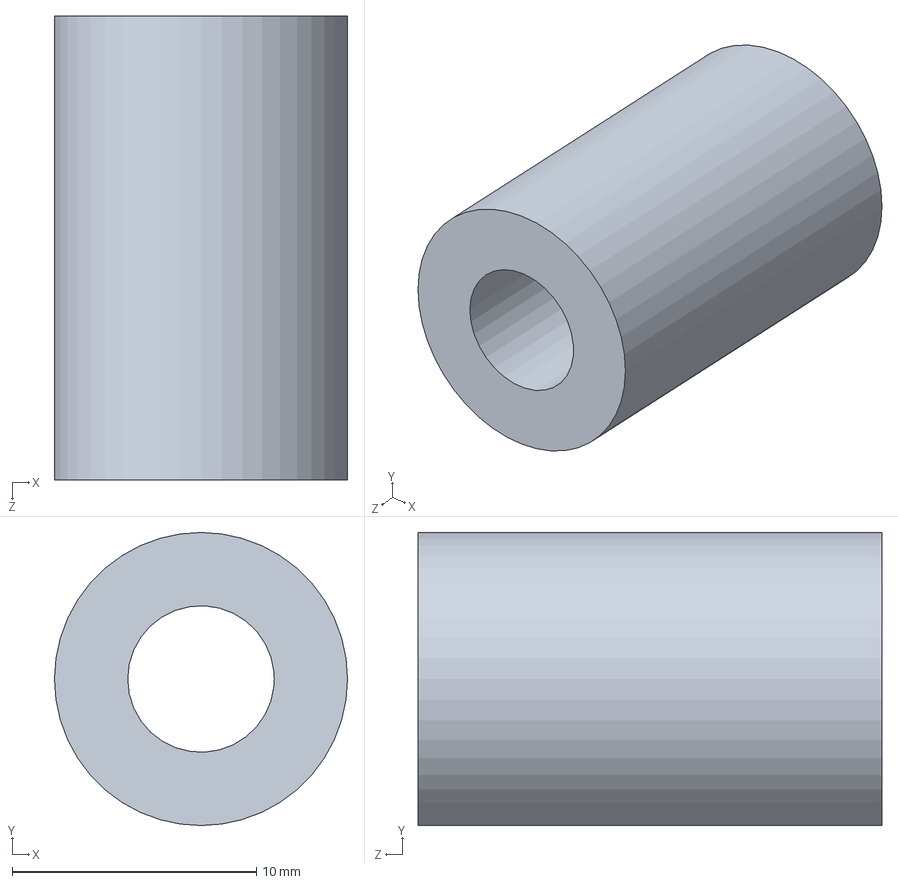
[picture p78: CAD file, 2022-04-09]
Machine/6mm滑杆直线轴承.SLDPRT
12.0 x 12.0 x 19.0 mm
