h13-0/RoboCup/Machine/机械爪简化.SLDPRT

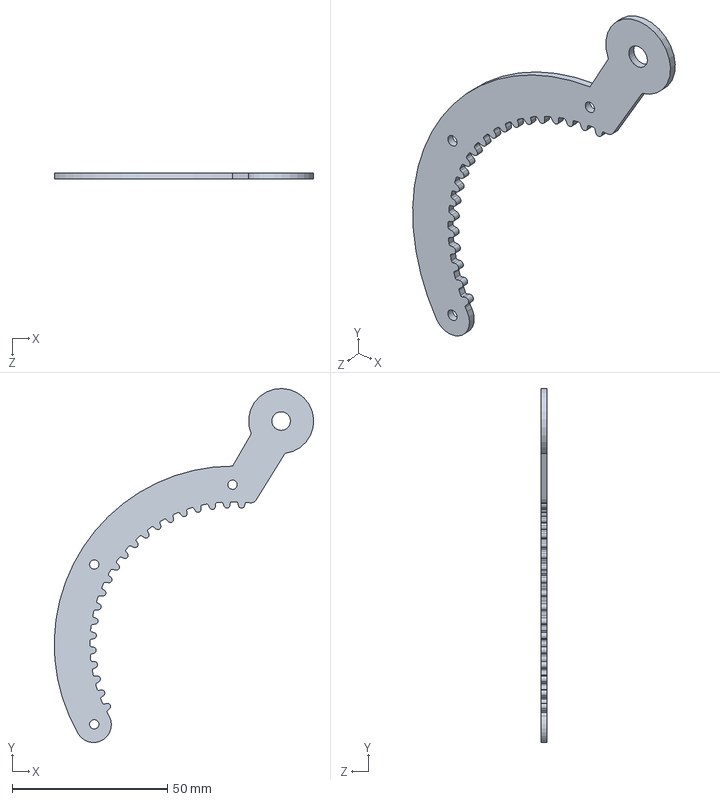
[picture p79: CAD file, 2021-10-01]
Machine/机械爪简化.SLDPRT
83.6 x 114.1 x 2.00 mm
