h13-0/RoboCup/Machine/机械爪中间片.SLDPRT

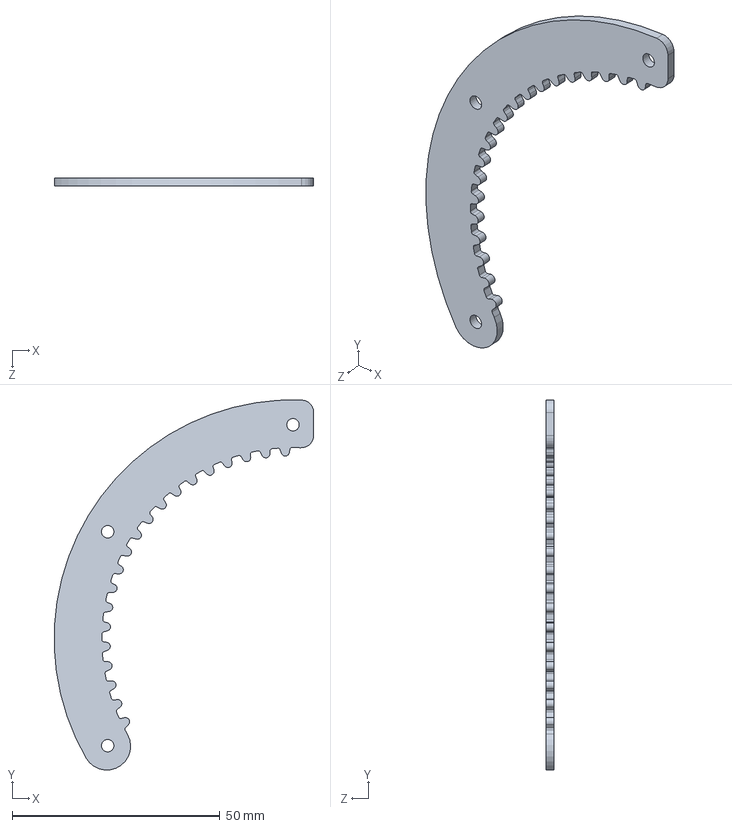
[picture p80: CAD file, 2021-10-01]
Machine/机械爪中间片.SLDPRT
62.5 x 89.1 x 2.00 mm
