h13-0/RoboCup/Machine/舵机云台中心圆盘转大圆盘底盘.SLDPRT

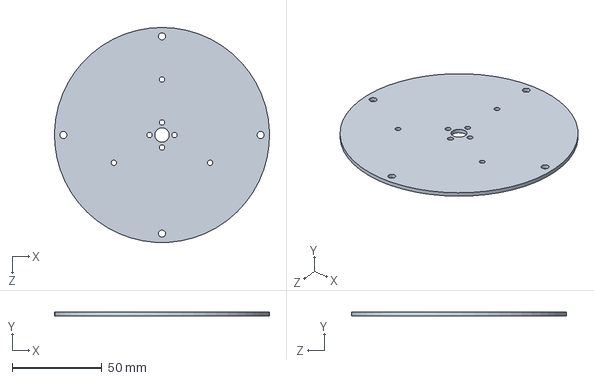
[picture p81: CAD file, 2021-09-02]
Machine/舵机云台中心圆盘转大圆盘底盘.SLDPRT
119.9 x 2.00 x 120.0 mm
