h13-0/RoboCup/Machine/舵机云台中心圆盘.SLDPRT

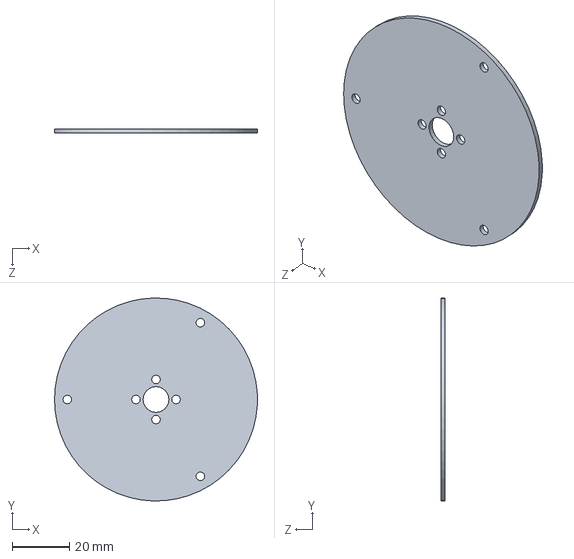
[picture p82: CAD file, 2021-09-02]
Machine/舵机云台中心圆盘.SLDPRT
71.0 x 71.0 x 1.50 mm
