h13-0/RoboCup/Machine/主动轮外齿轮.SLDPRT

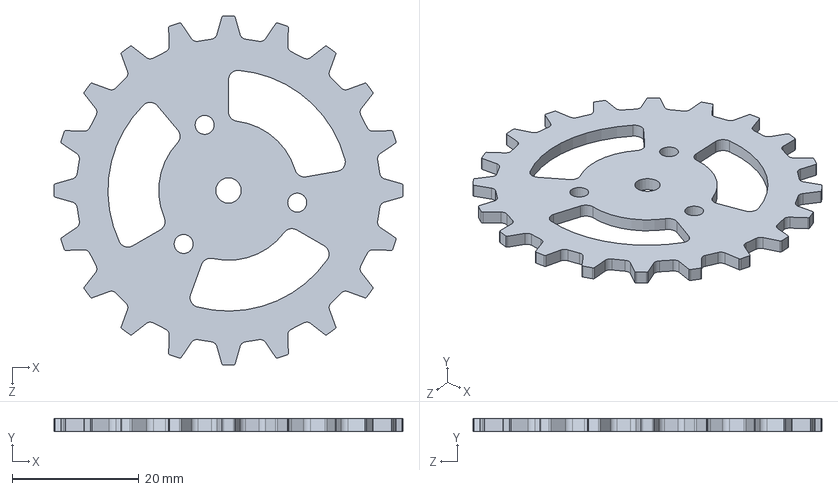
[picture p83: CAD file, 2021-09-02]
Machine/主动轮外齿轮.SLDPRT
55.0 x 2.00 x 55.0 mm
