h13-0/RoboCup/Machine/链条链节.SLDPRT

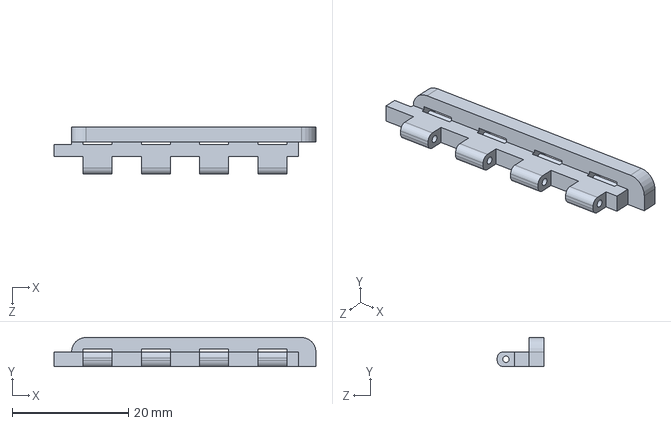
[picture p84: CAD file, 2021-09-02]
Machine/链条链节.SLDPRT
45.0 x 5.00 x 8.00 mm
