h13-0/RoboCup/Machine/主动轮联轴器.SLDPRT

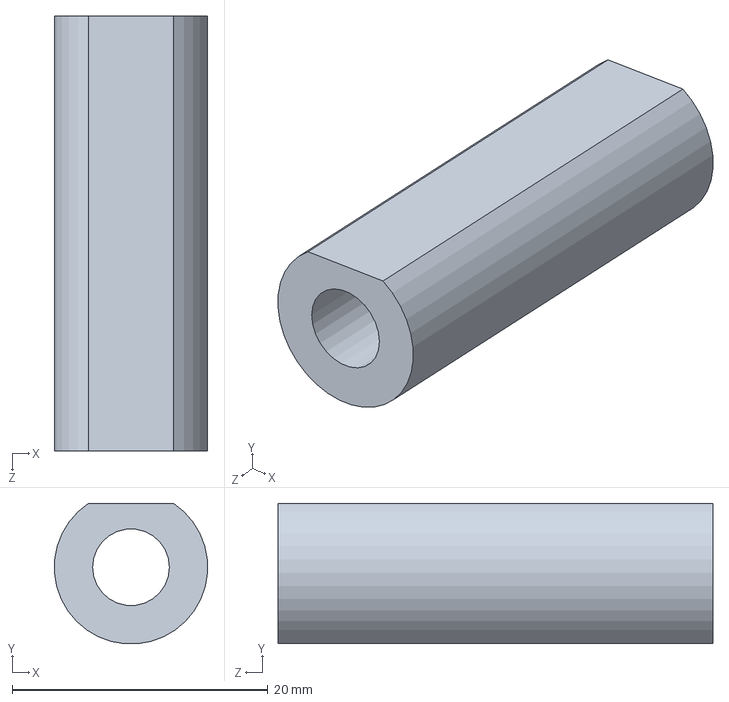
[picture p86: CAD file, 2021-09-02]
Machine/主动轮联轴器.SLDPRT
12.0 x 11.0 x 34.0 mm
