h13-0/RoboCup/Machine/机械臂连接板.SLDPRT

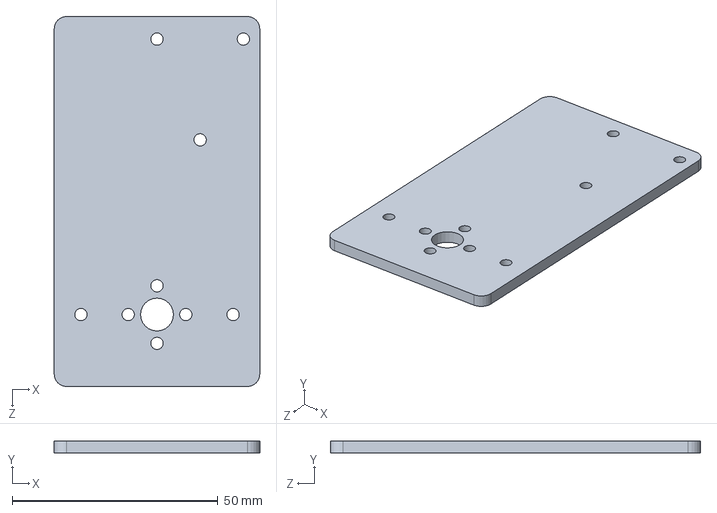
[picture p87: CAD file, 2021-08-29]
Machine/机械臂连接板.SLDPRT
50.0 x 3.00 x 90.0 mm
