h13-0/RoboCup/Machine/丝杆底支架.SLDPRT

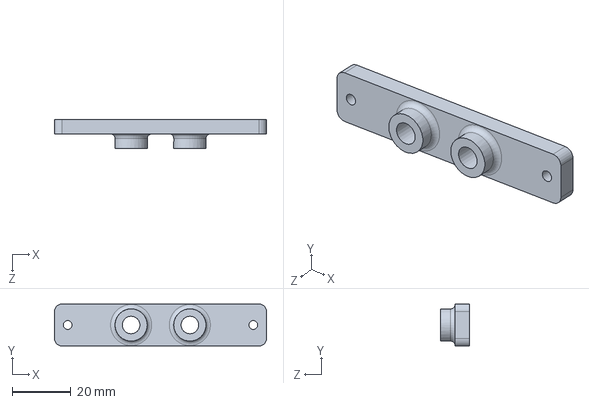
[picture p88: CAD file, 2021-08-29]
Machine/丝杆底支架.SLDPRT
72.2 x 14.3 x 10.0 mm
