h13-0/RoboCup/Machine/5转8联轴器.SLDPRT

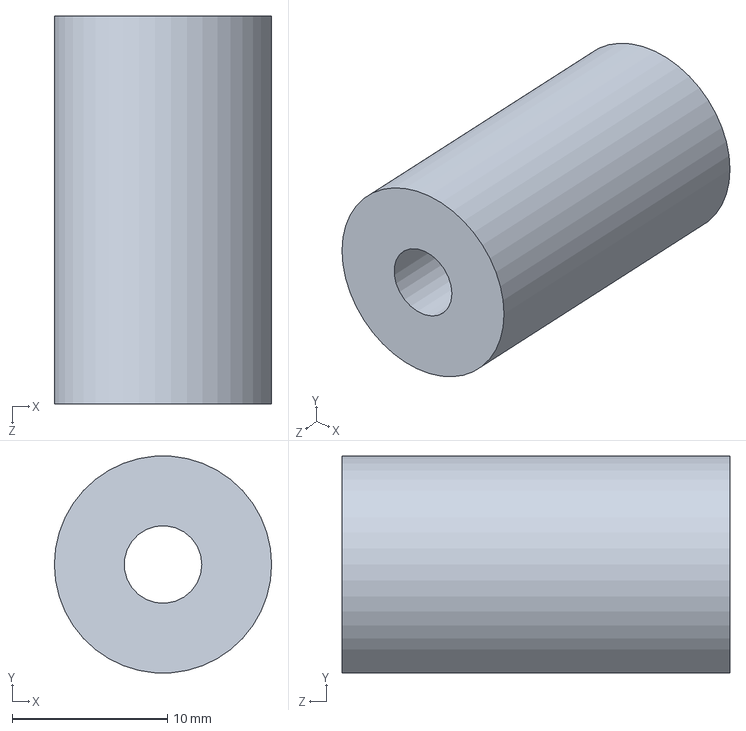
[picture p89: CAD file, 2021-08-29]
Machine/5转8联轴器.SLDPRT
14.0 x 14.0 x 25.0 mm
