h13-0/RoboCup/Machine/摄像头支架.SLDPRT

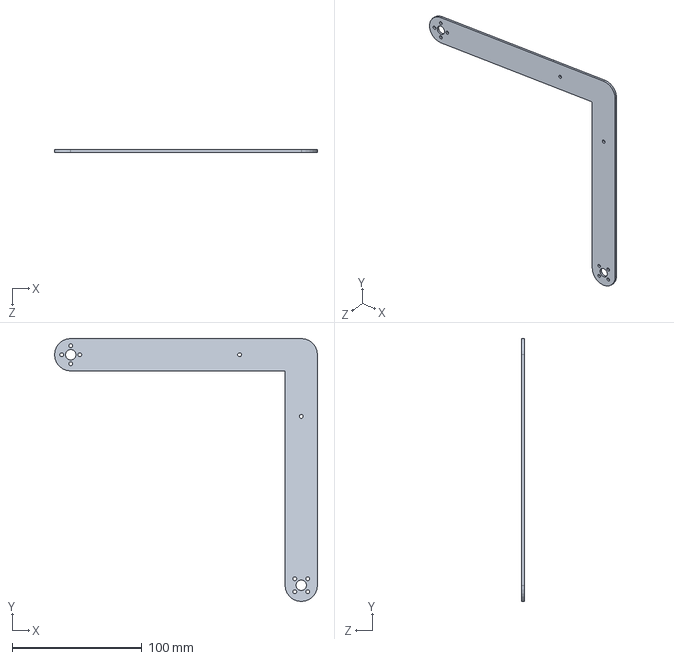
[picture p90: CAD file, 2021-08-29]
Machine/摄像头支架.SLDPRT
202.5 x 202.5 x 2.00 mm
