h13-0/RoboCup/Machine/舵机支架.SLDPRT

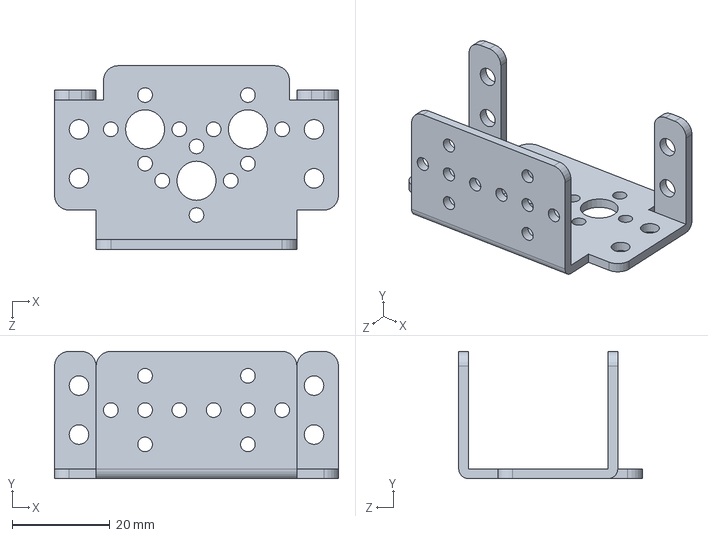
[picture p91: CAD file, 2021-08-29]
Machine/舵机支架.SLDPRT
58.0 x 26.0 x 37.5 mm
