h13-0/RoboCup/Machine/云台轴承.SLDPRT

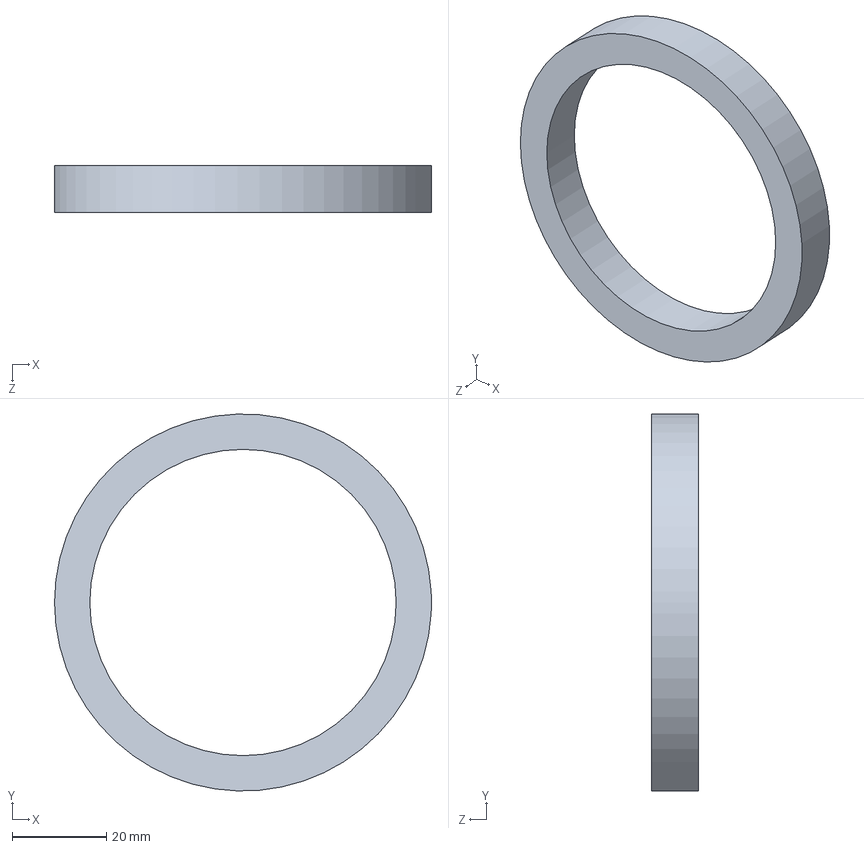
[picture p92: CAD file, 2021-08-23]
Machine/云台轴承.SLDPRT
80.0 x 80.0 x 10.0 mm
