h13-0/RoboCup/Machine/机械爪基座.SLDPRT

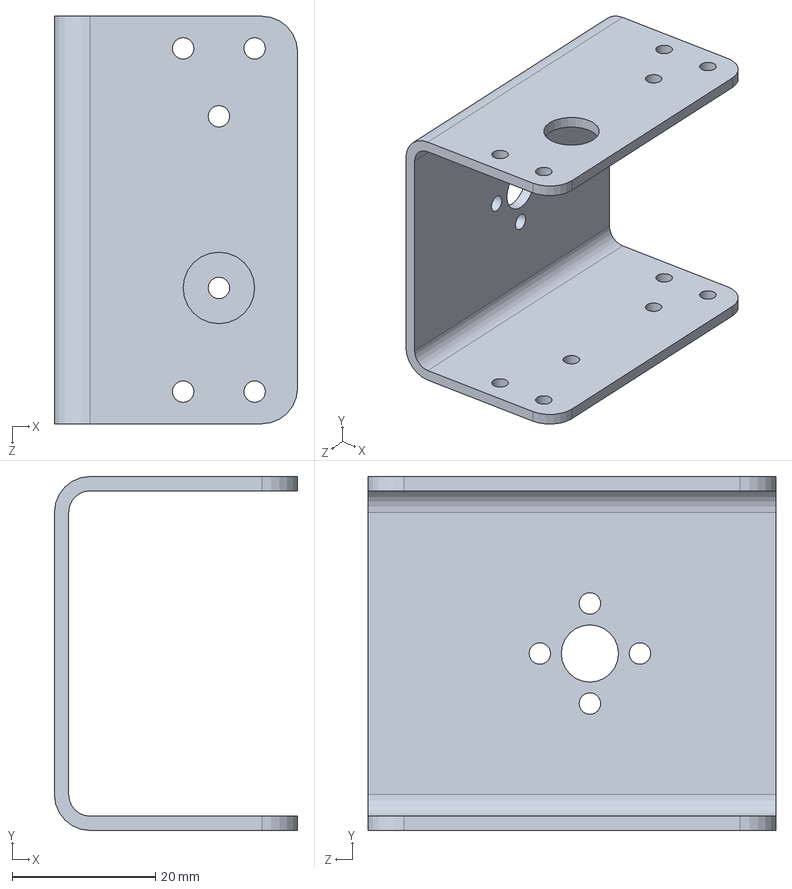
[picture p93: CAD file, 2021-08-15]
Machine/机械爪基座.SLDPRT
34.0 x 49.5 x 57.0 mm
