h13-0/RoboCup/Machine/同步带轴承.SLDPRT

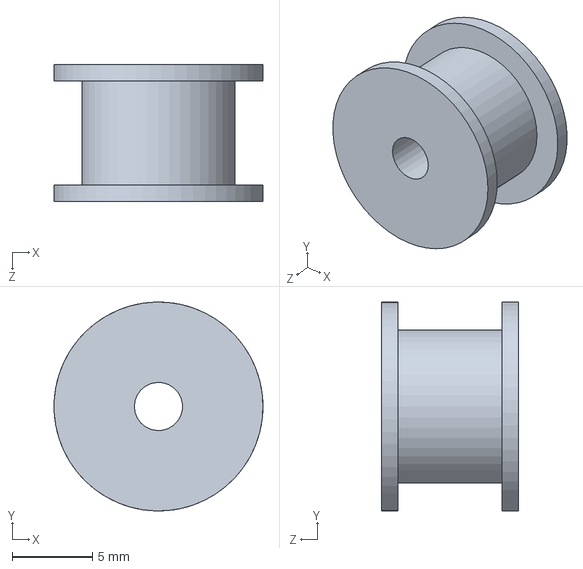
[picture p94: CAD file, 2021-08-15]
Machine/同步带轴承.SLDPRT
13.0 x 13.0 x 8.50 mm
