h13-0/RoboCup/Machine/机械臂杆件140mm.SLDPRT

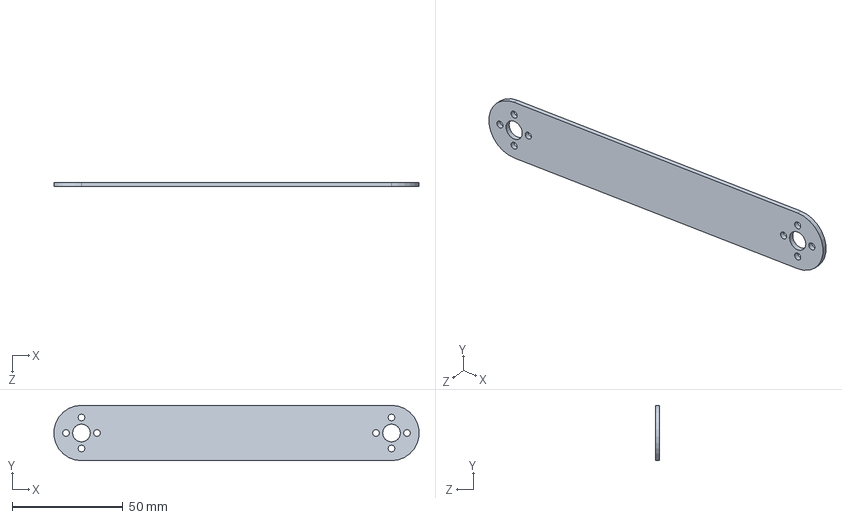
[picture p95: CAD file, 2021-08-15]
Machine/机械臂杆件140mm.SLDPRT
164.8 x 25.0 x 2.00 mm
