h13-0/RoboCup/Machine/一字件.SLDPRT

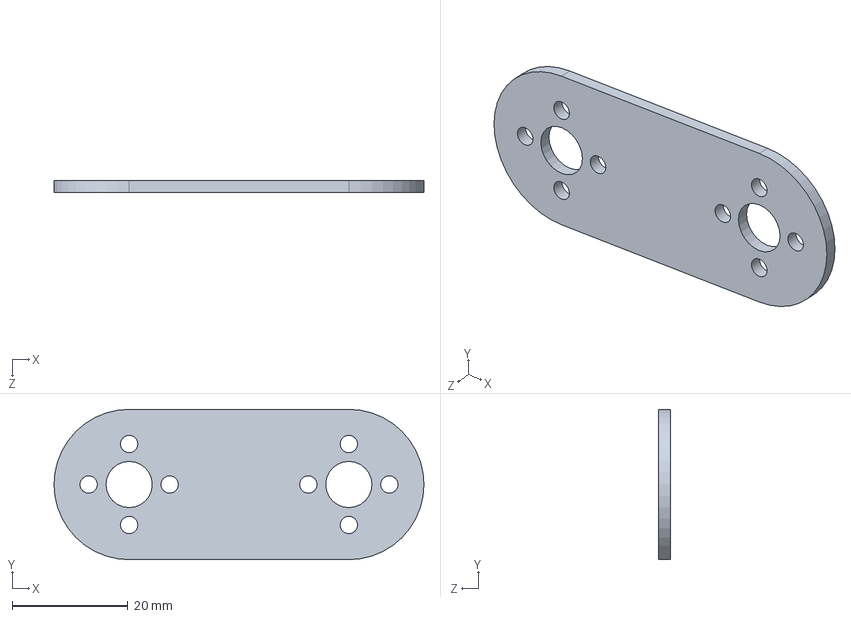
[picture p96: CAD file, 2021-08-15]
Machine/一字件.SLDPRT
64.0 x 26.0 x 2.00 mm
