h13-0/RoboCup/Machine/舵机.SLDPRT

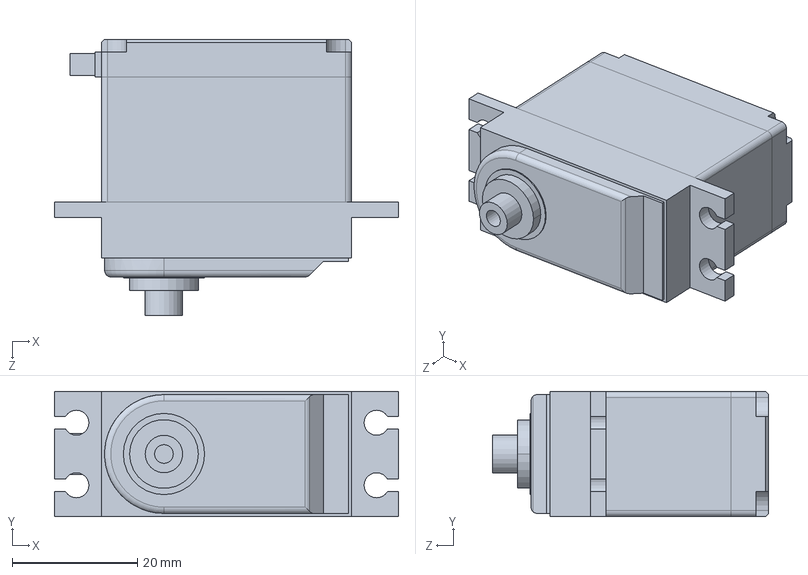
[picture p97: CAD file, 2021-08-15]
Machine/舵机.SLDPRT
55.0 x 20.0 x 44.2 mm
