h13-0/RoboCup/Machine/机械臂云台轴承支架.SLDPRT

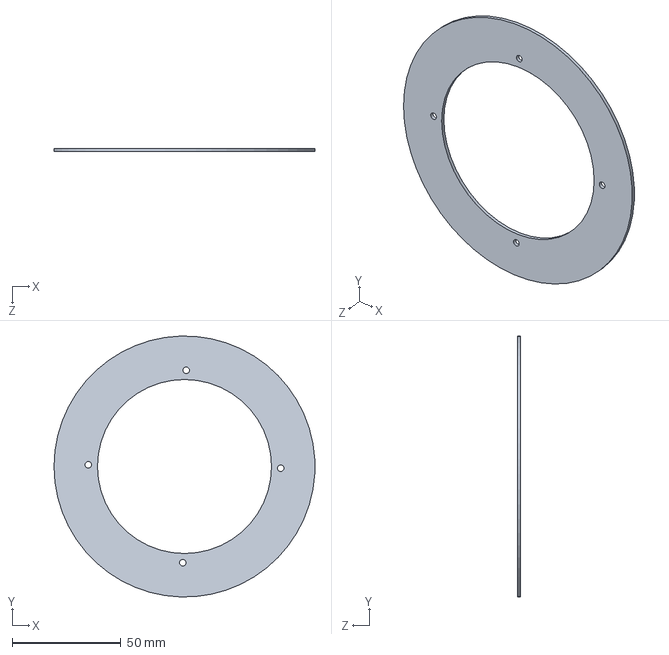
[picture p98: CAD file, 2021-08-15]
Machine/机械臂云台轴承支架.SLDPRT
120.0 x 119.9 x 1.50 mm
