h13-0/RoboCup/Machine/丝杆螺母.SLDPRT

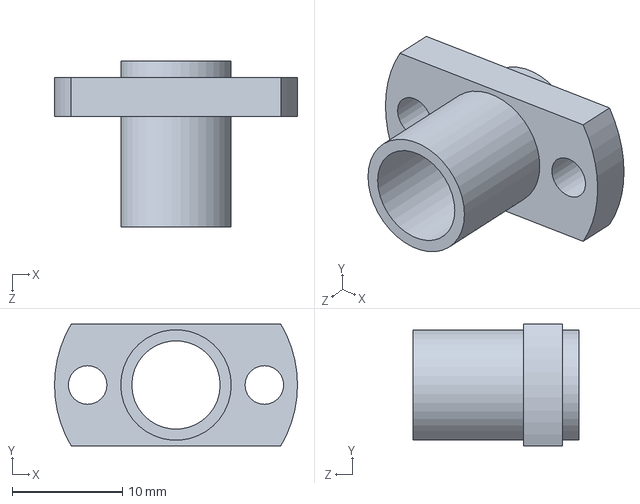
[picture p99: CAD file, 2021-08-15]
Machine/丝杆螺母.SLDPRT
22.0 x 11.0 x 15.0 mm
