h13-0/RoboCup/Machine/铝型材2040x60mm.SLDPRT

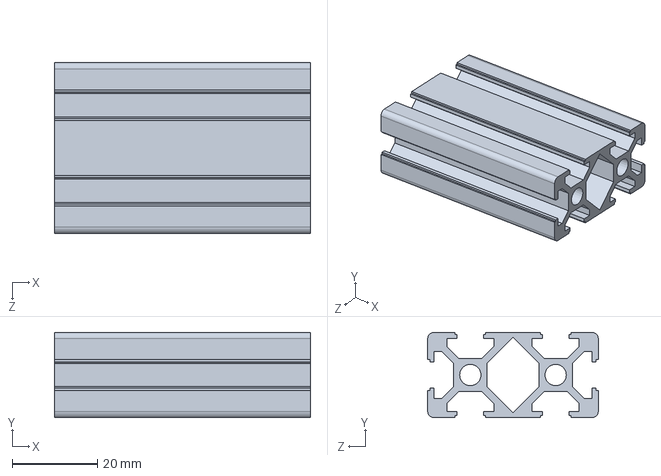
[picture p100: CAD file, 2021-08-14]
Machine/铝型材2040x60mm.SLDPRT
60.0 x 20.0 x 40.0 mm
