h13-0/RoboCup/Machine/旋转云台旋转盘.SLDPRT

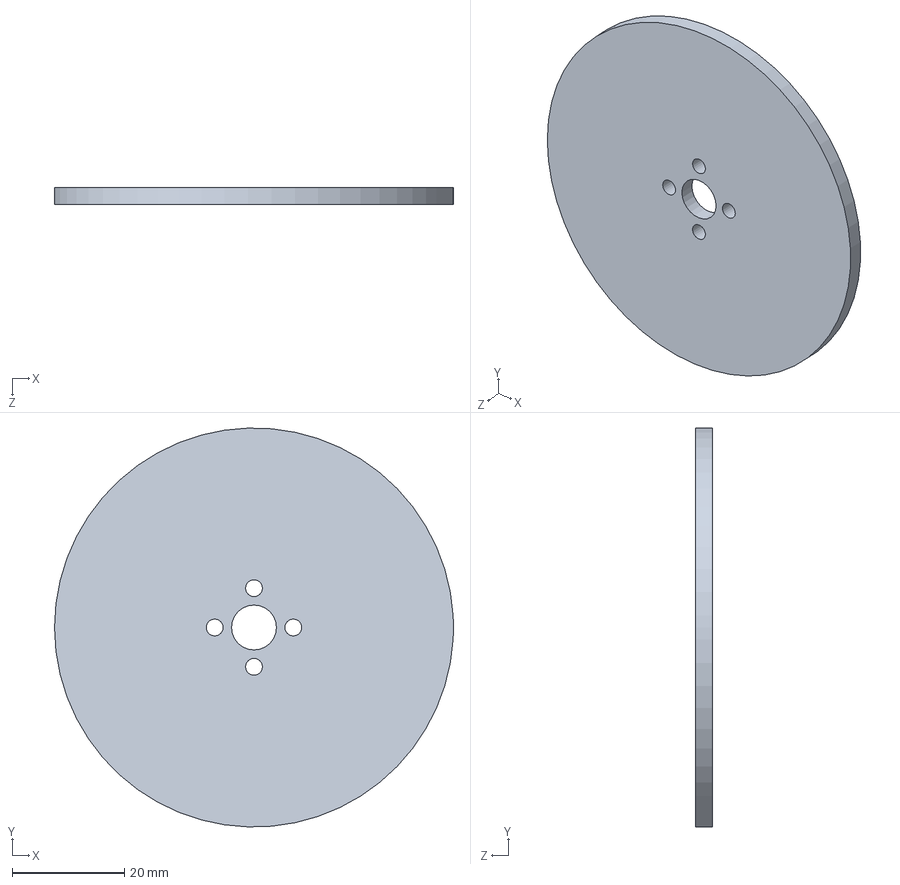
[picture p101: CAD file, 2021-08-10]
Machine/旋转云台旋转盘.SLDPRT
71.0 x 71.0 x 3.00 mm
