h13-0/RoboCup/STM32/Src/App/ArmControl/ArmControl.h

/*
 * ArmControl.h
 *
 *  Created on: 2021Äê8ÔÂ25ÈÕ
 *      Author: h13
 */

#ifndef APP_ARMCONTROL_ARMCONTROL_H_
#define APP_ARMCONTROL_ARMCONTROL_H_

#include <stdint.h>
#include "ports.h"

//#include "MechanicalArm.h"
#include "LiftingPlatform.h"

#endif /* APP_ARMCONTROL_ARMCONTROL_H_ */
