h13-0/RoboCup/STM32/Src/Drivers/WT101/WT101.c

/*
 * WT101.c
 *
 *  Created on: 2021Äê6ÔÂ22ÈÕ
 *      Author: h13
 */
#include "WT101.h"
#include "ports.h"

#define Clockwise     0
#define AntiClockwise 1
#define PositiveDirection Clockwise

#define CALSW  (0x76)
#define RATE   (0x03)
#define BAUD   (0x04)
//#define GX     (0x37)
//#define GY     (0x38)
#define GZ     (0x39)
//#define Roll   (0x3d)
//#define Pitch  (0x3e)
#define Yaw    (0x3f)

#if(DirectionSensorModel == WT101_InSerialMode)

struct WT101BufferStatusStructure
{
	uint8_t header      : 1;
	uint8_t regStatus   : 1;
	uint8_t regType     : 1;
	uint8_t bufferIndex : 5;
};

static struct WT101BufferStatusStructure status = {0, 0, 0, 0};

#define Reset 0
#define Set   1

#define AngularSpeed 0
#define EulerAngle   1

static uint8_t buffer[4] = { 0x00 };
static int16_t rawYawData = 0;
static int16_t rawYawVelocityData = 0;
static int16_t rawTemperatureData = 0;

/**
 * @brief: WT101 Serial Handler.
 * @param: data.
 */
void WT101_Handler(uint8_t data)
{
	//Check Header (0x55).
	if((data == 0x55) && (status.header == Reset))
	{
		status.header = Set;
		return;
	}

	//Check register (0x52 -> Angular Speed).
	if((data == 0x52) && (status.regStatus == Reset))
	{
		if(status.header == Set)
		{
			status.regStatus = Set;
			status.regType = AngularSpeed;
		} else {
			status = (struct WT101BufferStatusStructure){ 0 };
		}
		return;
	}

	//Check register (0x53 -> Eular Angular).
	if((data == 0x53) && (status.regStatus == Reset))
	{
		if(status.header == Set)
		{
			status.regStatus = Set;
			status.regType = EulerAngle;
		} else {
			//Reset status.
			status = (struct WT101BufferStatusStructure){ 0 };
		}
		return;
	}

	//Receive data when the header and register states are Set, otherwise reset status.
	if((status.header == Set) && (status.regStatus == Set))
	{
		if((status.bufferIndex > 3) && (status.bufferIndex < 8))
		{
			buffer[status.bufferIndex - 4] = data;
		} else if(status.bufferIndex == 8)
		{
			uint8_t sum = 0;
			for(uint8_t index = 0; index < 4; index ++)
			{
				sum += buffer[index];
			}

			sum = sum + 0x55 + 0x52 + status.regType;

			if(sum == data)
			{
				if(status.regType == AngularSpeed)
				{
					rawYawVelocityData = buffer[0] | buffer[1] << 8;
				} else {
					rawYawData = buffer[0] | buffer[1] << 8;
					rawTemperatureData = buffer[2] | buffer[3] << 8;
				}
			}

			//Reset status.
			status = (struct WT101BufferStatusStructure){ 0 };
			return;
		}

		status.bufferIndex ++;
	} else {
		//Reset status.
		status = (struct WT101BufferStatusStructure){ 0 };
	}
}

/**
 * @brief: Reset yaw value to zero.
 */
void ResetYaw(void)
{
	WT101_SerialSend(0xff);
	WT101_SerialSend(0xaa);
	WT101_SerialSend(CALSW);
	WT101_SerialSend(0x00);
	WT101_SerialSend(0x00);
}

/**
 * @brief: Set WT101 Return Rate.
 * @note:
 * 		**This will not take effect until WT101 is repowered**
 */
void SetWT101_ReturnRateTo(WT101_ReturnRate_t Rate)
{
	WT101_SerialSend(0xff);
	WT101_SerialSend(0xaa);
	WT101_SerialSend(RATE);
	WT101_SerialSend(Rate);
	WT101_SerialSend(0x00);
}

/**
 * @brief:  Get Yaw value.
 * @return: Yaw value in angle.
 */
__attribute__((always_inline)) inline float GetYawValue(void)
{
#if(PositiveDirection == Clockwise)
	return - rawYawData * 180.0 / 32768;
#else
	return rawYawData * 180.0 / 32768;
#endif
}

/**
 * @brief:  Get Yaw Velocity value.
 * @return: Yaw Velocity value in angle per second.
 */
__attribute__((always_inline)) inline float GetYawVelocity(void)
{
#if(PositiveDirection == Clockwise)
	return - rawYawVelocityData * 2000.0 / 32768;
#else
	return rawYawVelocityData * 2000.0 / 32768;
#endif
}

/**
 * @brief:  Get Temperature value.
 * @return: Temperature value in centigrade.
 */
__attribute__((always_inline)) inline float GetTemperature(void)
{
	return rawTemperatureData / 100.0;
}

#else

/**
 * @brief: Reset yaw value to zero.
 */
void ResetYaw(void)
{
	uint8_t data[] = { 0x00, 0x00 };
	I2C_WriteLen(WT101_I2C_Address, CALSW, 2, data);
}

/**
 * @brief: Set WT101 Return Rate.
 * @note:
 * 		**This will not take effect until WT101 is repowered**
 */
void SetWT101_ReturnRateTo(WT101_ReturnRate_t Rate)
{
	uint8_t data[] = { Rate, 0x00};
	I2C_WriteLen(WT101_I2C_Address, RATE, 2, data);
}

/**
 * @brief:  Get Yaw value.
 * @return: Yaw value in angle.
 */
float GetYawValue(void)
{
	uint8_t data[2] = { 0 };
	I2C_ReadLen(WT101_I2C_Address, Yaw, 2, data);
	int16_t tempData = (data[0] | data[1] << 8);
#if(PositiveDirection == Clockwise)
	return - tempData * 180.0 / 32768;
#else
	return tempData * 180.0 / 32768;
#endif
}

/**
 * @brief:  Get Yaw Velocity value.
 * @return: Yaw Velocity value in angle per second.
 */
float GetYawVelocity(void)
{
	uint8_t data[2] = { 0 };
	I2C_ReadLen(WT101_I2C_Address, GZ, 2, data);
	int16_t tempData = (data[0] | data[1] << 8);
#if(PositiveDirection == Clockwise)
	return - tempData * 2000.0 / 32768;
#else
	return tempData * 2000.0 / 32768;
#endif
}

/**
 * @brief:  Get Temperature value.
 * @return: Temperature value in centigrade.
 */
float GetTemperature(void)
{
	return 0;
}

#endif
