h13-0/RoboCup/STM32/Src/App/Timer/Timer.c

/*
 * Timer.c
 *
 *  Created on: 2021Äê6ÔÂ8ÈÕ
 *      Author: h13
 */

#include "RobotConfigs.h"
#include "ArmControl.h"
#include "Timer.h"

#include "MotionControl.h"
#include "Stepper.h"
#include "DF_PlayerMini.h"

/**
 * @brief: Timer Interrupt Handler.
 * @note:
 * 		Responsible for PID calculation.
 * 		**Call frequency: 100Hz.**
 */
__attribute__((always_inline)) inline void TimerHandler(void)
{
	SpeedPIDCalculateHandler();
	DirectionPIDCalculateHandler();
	ForwardPIDCalculateHandler();
}

/**
 * @brief: Timer for LVGL and Voice queue.
 * @note:
 * 		**Call frequency: 30Hz.**
 */
__attribute__((always_inline)) inline void UI_VoiceTimerHandler(void)
{
	DF_PlayerVoiceQueueTimerHandler();
}

#if(ArmType == LiftingPlatform)

/**
 * @brief: Timer for Stepper motor pulse.
 * @note:
 * 		**Call frequency: 2000Hz.**
 */
__attribute__((always_inline)) inline void StepperTimerInterruptHandler(void)
{
	SteperTimerHandler();
}

#endif
