h13-0/RoboCup/STM32/Src/Platform/SPI/SPI.h

/*
 * SPI.h
 *
 *  Created on: 2021Äê6ÔÂ5ÈÕ
 *      Author: h13
 */

#ifndef PLATFORM_SPI_SPI_H_
#define PLATFORM_SPI_SPI_H_

#include <stdint.h>

typedef enum
{
	SPI_OK,
	SPI_Busy,
	SPI_TransmissionTimeout,
} SPI_Error_t;

/**
 * @brief: Initialize the SPI interface.
 * @note:  If multiple devices are mounted under the SPI interface, be aware of SPI initialization sequence and repeated initialization issues.
 *
 */
void SPIInit(void);

/**
 * @brief:  SPI write 8-bit data.
 * @param:  data.
 * @return: Status.
 */
SPI_Error_t SPIWriteByte(uint8_t data);

/**
 * @group: Set and Reset Pins of LCD.
 */
void LCDSetRST(void);

void LCDResetRST(void);

void LCDSetCS(void);

void LCDResetCS(void);

void LCDSetDC(void);

void LCDResetDC(void);

#endif /* PLATFORM_SPI_SPI_H_ */
