h13-0/RoboCup/STM32/Src/Drivers/VL6180X/Platform/vl6180x_platform.h

/*******************************************************************************
################################################################################
#
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
#------------------------------------------------------------------------------
#                             Imaging Division
################################################################################
********************************************************************************/

#ifndef SRC_VL6180X_PLATFORM_VL6180X_PLATFORM_H_
#define SRC_VL6180X_PLATFORM_VL6180X_PLATFORM_H_

#include "vl6180x_def.h"

#include "I2C.h"
#include "GPIO.h"

#define VL6180x_SINGLE_DEVICE_DRIVER 	0
#define VL6180x_RANGE_STATUS_ERRSTRING  0
#define VL6180X_SAFE_POLLING_ENTER 		0
#define VL6180X_LOG_ENABLE			    0


#define VL6180x_DEV_DATA_ATTR
#define ROMABLE_DATA


#if VL6180X_LOG_ENABLE
/*  dot not include non ansi here trace was a case :( */
#ifdef TRACE
#include "diag/trace.h"
#define LOG_GET_TIME()  HAL_GetTick()
#else
/* these is nto stm32 vl6180x GNuArm eclpse build*/
#define trace_printf(...) (void)0
#define LOG_GET_TIME() (int)0 /* add your code here expect to be an integer native (%d) type  value  */
#endif



#define LOG_FUNCTION_START(fmt, ... ) \
    trace_printf("beg %s start @%d\t" fmt "\n", __func__, LOG_GET_TIME(), ##__VA_ARGS__)

#define LOG_FUNCTION_END(status)\
        trace_printf("end %s @%d %d\n", __func__, LOG_GET_TIME(), (int)status)

#define LOG_FUNCTION_END_FMT(status, fmt, ... )\
        trace_printf("End %s @%d %d\t"fmt"\n" , __func__, LOG_GET_TIME(), (int)status, ##__VA_ARGS__)

#define VL6180x_ErrLog(msg, ... )\
    do{\
        trace_printf("ERR in %s line %d\n" msg, __func__, __LINE__, ##__VA_ARGS__);\
    }while(0)

#else /* VL6180X_LOG_ENABLE no logging */

	#define LOG_FUNCTION_START(...) (void)0
	#define LOG_FUNCTION_END(...) (void)0
	#define LOG_FUNCTION_END_FMT(...) (void)0
    #define VL6180x_ErrLog(... ) (void)0
#endif


#if  VL6180x_SINGLE_DEVICE_DRIVER
    #error "VL6180x_SINGLE_DEVICE_DRIVER must be set"
#endif

typedef struct{
	struct VL6180xDevData_t Data;
	uint8_t I2cAddr;
	uint8_t DevID;

	// misc flags for application
    unsigned Present:1;
    unsigned Ready:1;

    // Platform variables
    GPIO_t   XshutIO;
} VL6180x_Dev_t;
typedef VL6180x_Dev_t* VL6180xDev_t;

#define VL6180xDevDataGet(dev, field) (dev->Data.field)
#define VL6180xDevDataSet(dev, field, data) (dev->Data.field)=(data)

//void DISP_ExecLoopBody(void);
//#define VL6180x_PollDelay(dev)   DISP_ExecLoopBody();
#define VL6180x_PollDelay(dev)   (void)0

void VL6180x_Reset(VL6180x_Dev_t* dev);

void VL6180x_Shutdown(VL6180x_Dev_t* dev);

void VL6180x_StartUp(VL6180x_Dev_t* dev);

#endif /* SRC_VL6180X_PLATFORM_VL6180X_PLATFORM_H_ */
