h13-0/RoboCup/STM32/Src/PrivateConfigs.h

/*
 * PrivateConfigs.h
 *
 *  Created on: 2021年8月9日
 *      Author: h13
 */

#ifndef PRIVATECONFIGS_H_
#define PRIVATECONFIGS_H_

#define TargetPhone                                  ("1101201120") //It's Fake.

#endif /* ROBOTCONFIGS_H_ */
