h13-0/RoboCup/ImageProcessing/HSV/RoboCupImageProcessing/Detectors/KiwiFruitDetector.hpp

#pragma once
#include <vector>
#include <opencv2/opencv.hpp>
#include <opencv2/highgui/highgui_c.h>
#include "KiwiFruitDetectorConfigs.hpp"
#include "Detector.hpp"

namespace RoboCup
{
	class KiwiFruitDetector : public Detector
	{
	public:
		KiwiFruitDetector(const std::vector<h13::HSV_Threshold_t>& PositiveThresholds = { h13::HSV_Threshold(60, 80, 80, 180, 50, 255), h13::HSV_Threshold(45, 110, 22, 206, 15, 255) },
			const std::vector<h13::HSV_Threshold_t>& NegativeThresholds = { h13::HSV_Threshold(0, 51, 0, 26, 0, 255), h13::HSV_Threshold(0, 255, 0, 40, 0, 255) },
			const std::vector<h13::HSV_Threshold_t>& ReflectiveThresholds = { },
			float MinimumSize = 1300,
			float MinimunLengthWidthRatio = 0.65) noexcept
			: Detector(PositiveThresholds, NegativeThresholds, ReflectiveThresholds)
			, minimumSize(MinimumSize), minimunLengthWidthRatio(MinimunLengthWidthRatio) { };
		
#if defined(__USE_DETECTOR_CONFIGS__)
		KiwiFruitDetector(const KiwiFruitDetectorConfigs& configs) noexcept
			: Detector(configs.GetPositiveThresholds(), configs.GetNegativeThresholds(), configs.GetReflectiveThresholds())
			, minimumSize(configs.GetMinimumSize()), minimunLengthWidthRatio(configs.GetMinimumLengthWidthRatio()) { };
#endif
		
		~KiwiFruitDetector() { };
		std::vector<cv::RotatedRect> Detect(cv::InputArray InputBGR_Image, cv::InputArray InputHSV_FULL_Image = cv::noArray(), cv::OutputArray OutputFilledBinaryContours = cv::noArray()) noexcept;
	
	private:
		float minimumSize;
		float minimunLengthWidthRatio;
	};
}
