h13-0/RoboCup/STM32/Src/Drivers/VL6180X/Platform/vl6180x_types.h

/*
 * vl6180x_types.h
 *
 *  Created on: 2021年8月6日
 *      Author: h13
 */

#ifndef SRC_VL6180X_PLATFORM_VL6180X_TYPES_H_
#define SRC_VL6180X_PLATFORM_VL6180X_TYPES_H_

#include <stdint.h>
#include <stddef.h>

#endif /* SRC_VL6180X_PLATFORM_VL6180X_TYPES_H_ */
