h13-0/RoboCup/ImageProcessing/YoloFastest/yolo-fastest.cfg

[net]
batch=48
subdivisions=2
width=320
height=224
channels=3
momentum=0.949
decay=0.0005
angle=0
max_chart_loss=0.5
learning_rate=0.00003
burn_in=600
max_batches= 500000
policy=steps
steps=400000, 450000
scales=.1,.1


learning_rate=0.001
burn_in=4000
max_batches=500000
policy=steps
steps=400000,450000
scales=.1,.1

[convolutional]
filters=8
size=3
pad=1
stride=2
batch_normalize=1
activation=leaky


[convolutional]
filters=8
size=1
stride=1
pad=0
batch_normalize=1
activation=leaky

[convolutional]
groups=8
filters=8
size=3
stride=1
pad=1
batch_normalize=1
activation=leaky

[convolutional]
filters=4
size=1
stride=1
pad=0
batch_normalize=1
activation=linear


[convolutional]
filters=8
size=1
stride=1
pad=0
batch_normalize=1
activation=leaky

[convolutional]
groups=8
filters=8
size=3
stride=1
pad=1
batch_normalize=1
activation=leaky

[convolutional]
filters=4
size=1
stride=1
pad=0
batch_normalize=1
activation=linear


[dropout]
probability=.15

[shortcut]
from=-5
activation=linear

[convolutional]
filters=24
size=1
stride=1
pad=0
batch_normalize=1
activation=leaky

[convolutional]
groups=24
filters=24
size=3
pad=1
stride=2
batch_normalize=1
activation=leaky

[convolutional]
filters=8
size=1
stride=1
pad=0
batch_normalize=1
activation=linear


[convolutional]
filters=32
size=1
stride=1
pad=0
batch_normalize=1
activation=leaky

[convolutional]
groups=32
filters=32
size=3
stride=1
pad=1
batch_normalize=1
activation=leaky

[convolutional]
filters=8
size=1
stride=1
pad=0
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
pad=1
batch_normalize=1
activation=linear

[convolutional]
filters=96
size=5
groups=96
stride=1
pad=1
batch_normalize=1
activation=leaky

[convolutional]
filters=96
size=1
stride=1
pad=1
batch_normalize=1
activation=linear


[convolutional]
size=1
stride=1
pad=1
filters=42
activation=linear


[yolo]
mask = 3,4,5
anchors = 12, 18,  37, 49,  52,132, 115, 73, 119,199, 242,238
classes=9
num=6
jitter=.15
ignore_thresh = .5
truth_thresh = 1
random=0
scale_x_y = 1.0
iou_thresh=0.213
cls_normalizer=1.0
iou_normalizer=0.07
iou_loss=ciou
nms_kind=greedynms
beta_nms=0.6

[route]
layers = -7

[upsample]
stride = 2

[route]
layers=-1,80

[convolutional]
filters=120
size=5
groups=120
stride=1
pad=1
batch_normalize=1
activation=leaky

[convolutional]
filters=120
size=1
stride=1
pad=1
batch_normalize=1
activation=linear

[convolutional]
filters=120
size=5
groups=120
stride=1
pad=1
batch_normalize=1
activation=leaky

[convolutional]
filters=120
size=1
stride=1
pad=1
batch_normalize=1
activation=linear

[convolutional]
size=1
stride=1
pad=1
filters=42
activation=linear


[yolo]
mask = 0,1,2
anchors = 12, 18,  37, 49,  52,132, 115, 73, 119,199, 242,238
classes=9
num=6
jitter=.15
ignore_thresh = .5
truth_thresh = 1
random=0
scale_x_y = 1.00
iou_thresh=0.213
cls_normalizer=1.0
iou_normalizer=0.07
iou_loss=ciou
nms_kind=greedynms
beta_nms=0.6
